Board-Folk/TRS80IJP/Extras/TRSG3Mod/images/g3modboards_large.jpg

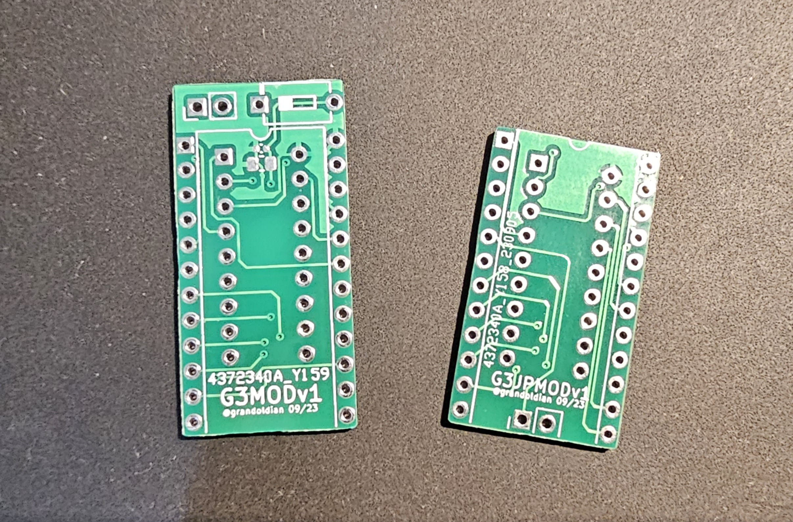
Extras/TRSG3Mod/images/g3modboards_large.jpg
