Board-Folk/TRS80IJP/v1.1/Kicad/TRS80IJP_CPU.kicad_sch

## KiCad design v1.1/Kicad/TRS80IJP_CPU.kicad_sch (2023-09-25)

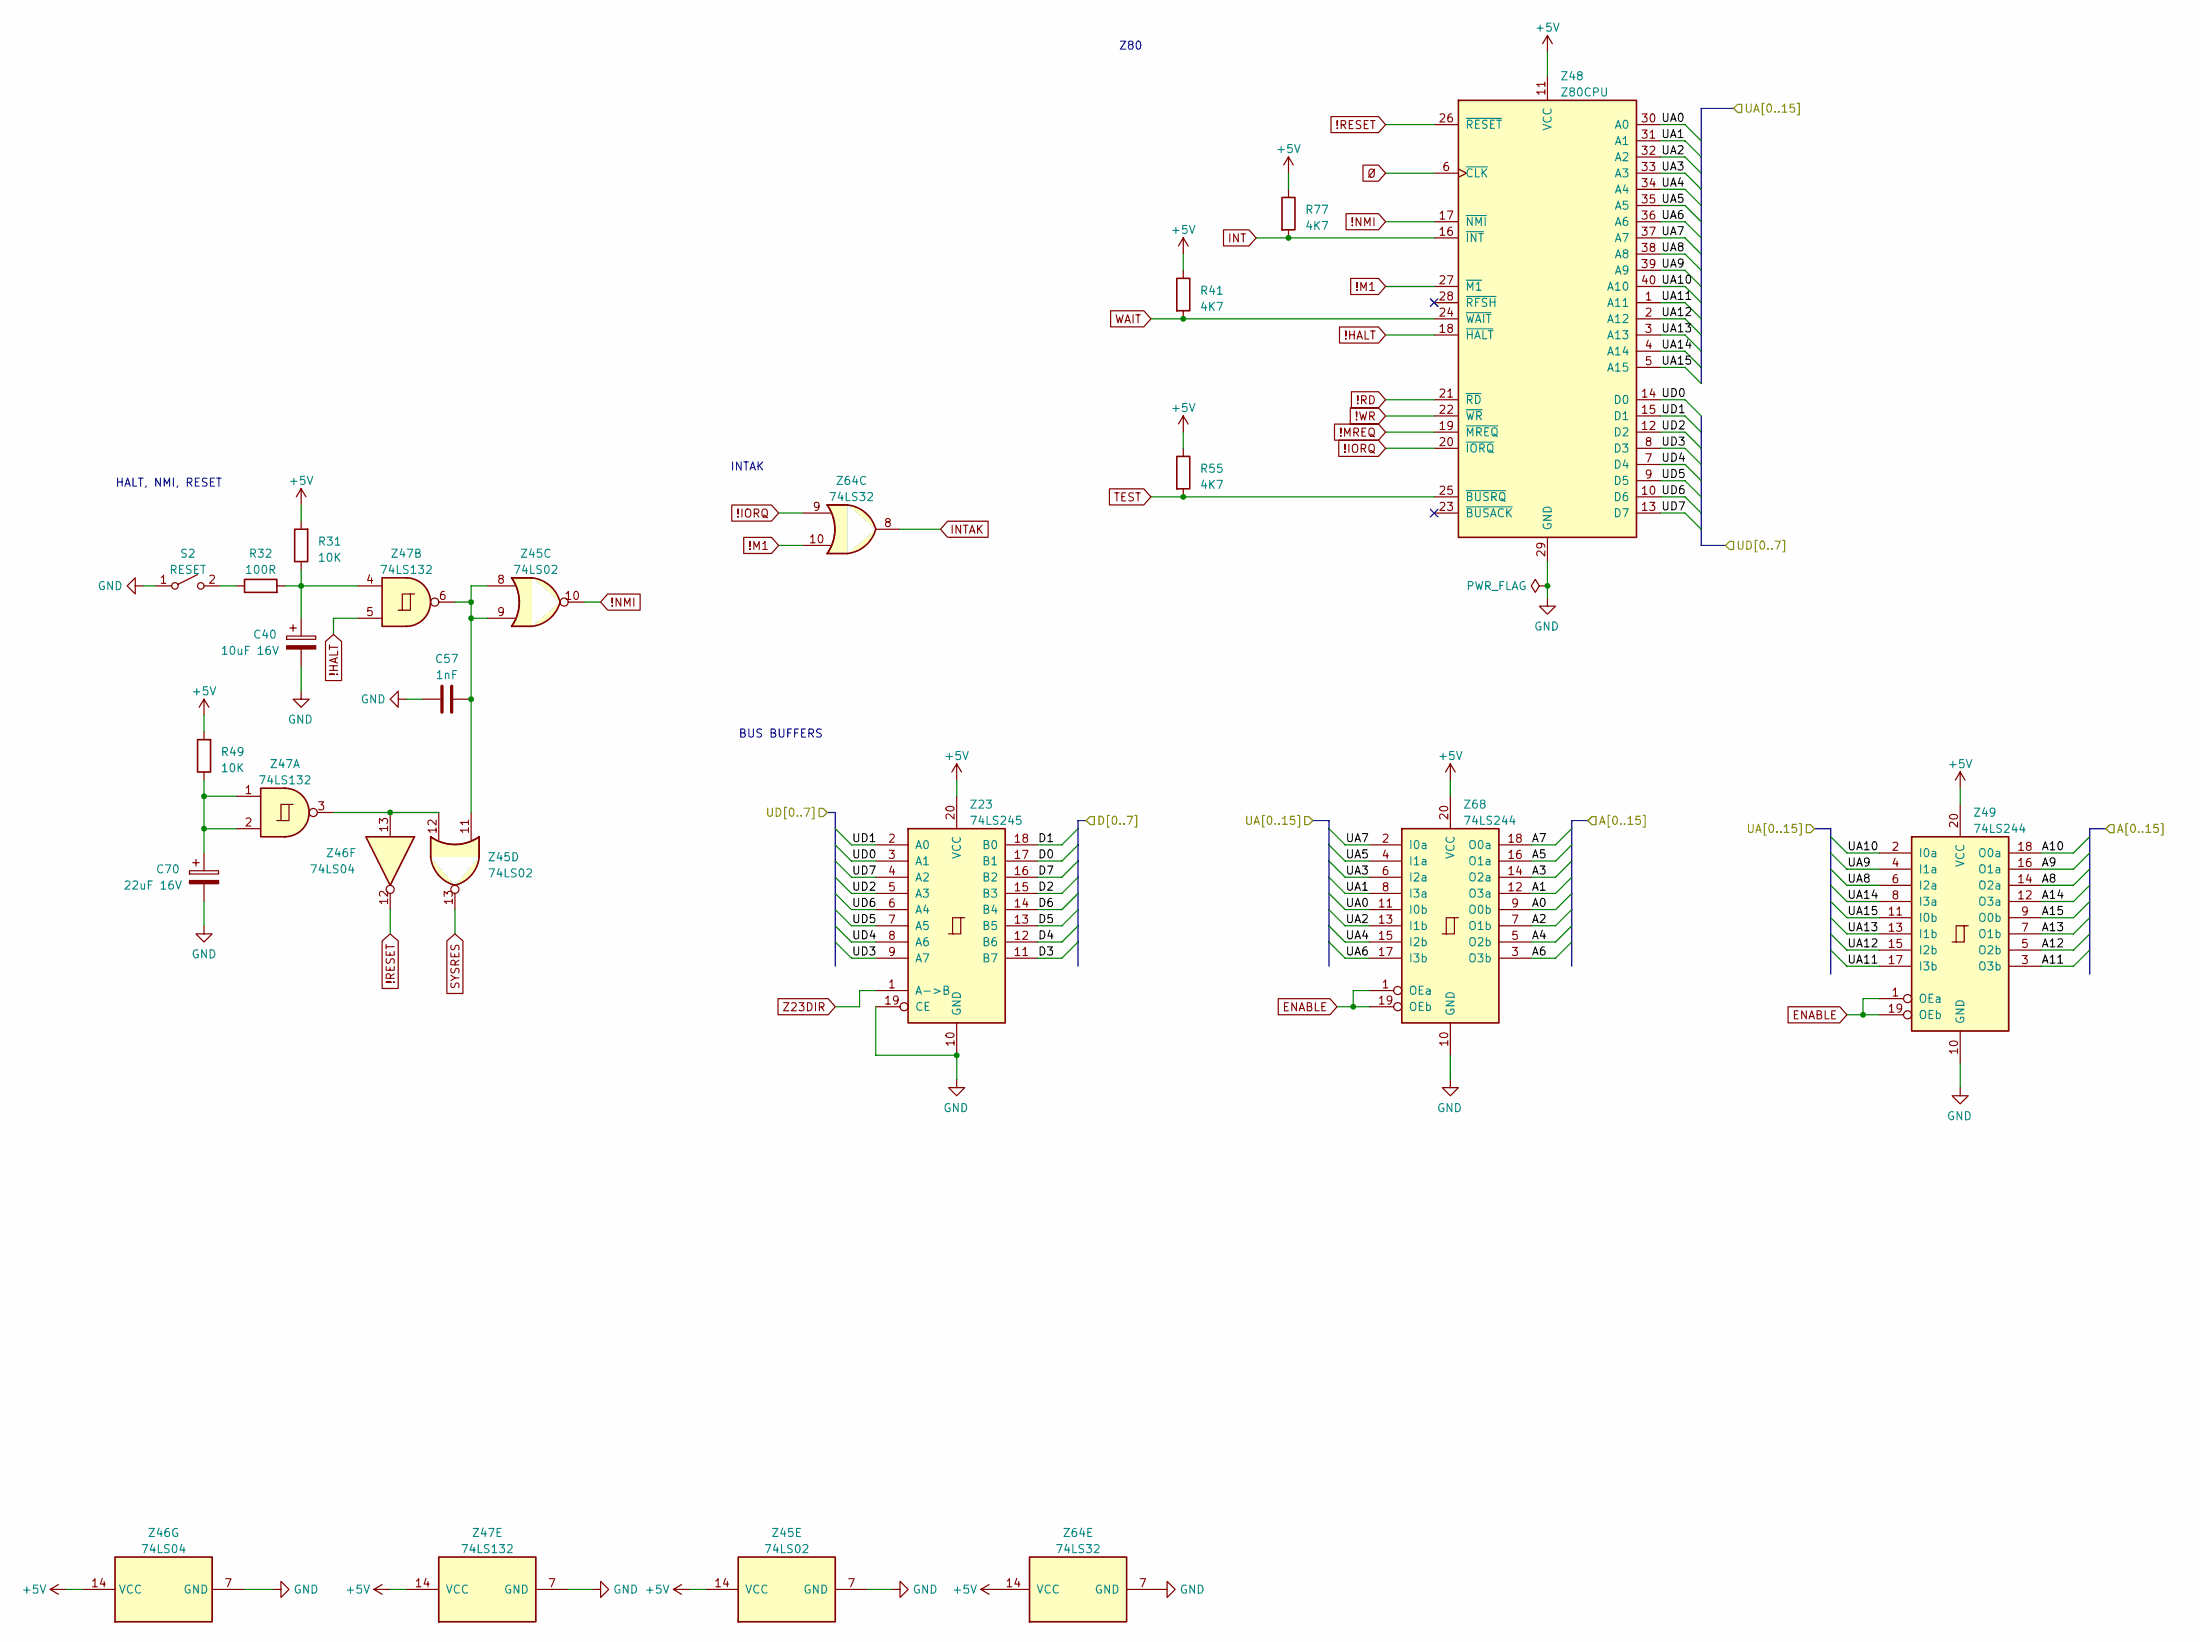
[picture p12: schematic TRS80IJP_CPU.kicad_sch]

Parts:
C40: 10uF 16V; CP_Radial_D5.0mm_P2.50mm
C57: 1nF; Ceramic Disc 2.5mm
C70: 22uF 16V; CP_Radial_D5.0mm_P2.50mm
R31, R49: 10K; Resistor 10.16mm
R32: 100R; Resistor 10.16mm
R41, R55, R77: 4K7; Resistor 10.16mm
S2: RESET; S2
Z23: 74LS245; DIP-20_W7.62mm
Z45: 74LS02; DIP-14_W7.62mm
Z46: 74LS04; DIP-14_W7.62mm
Z47: 74LS132; DIP-14_W7.62mm
Z48: Z80CPU; DIP-40_W15.24mm
Z49, Z68: 74LS244; DIP-20_W7.62mm
Z64: 74LS32; DIP-14_W7.62mm

Connections:
!HALT: Z47.5, Z48.18 (~HALT)
!IORQ: Z48.20 (~IORQ), Z64.9
!M1: Z48.27 (~M1), Z64.10
!MREQ: Z48.19 (~MREQ)
!NMI: Z45.10, Z48.17 (~NMI)
!RD: Z48.21 (~RD)
!RESET: Z46.12, Z48.26 (~RESET)
!WR: Z48.22 (~WR)
+5V: R31.2, R41.1, R49.2, R55.1, R77.1, Z23.20 (VCC), Z45.14 (VCC), Z46.14 (VCC), Z47.14 (VCC), Z48.11 (VCC), Z49.20 (VCC), Z64.14 (VCC), Z68.20 (VCC)
A0: Z68.9 (O0b)
A1: Z68.12 (O3a)
A2: Z68.7 (O1b)
A3: Z68.14 (O2a)
A4: Z68.5 (O2b)
A5: Z68.16 (O1a)
A6: Z68.3 (O3b)
A7: Z68.18 (O0a)
A8: Z49.14 (O2a)
A9: Z49.16 (O1a)
A10: Z49.18 (O0a)
A11: Z49.3 (O3b)
A12: Z49.5 (O2b)
A13: Z49.7 (O1b)
A14: Z49.12 (O3a)
A15: Z49.9 (O0b)
D0: Z23.17 (B1)
D1: Z23.18 (B0)
D2: Z23.15 (B3)
D3: Z23.11 (B7)
D4: Z23.12 (B6)
D5: Z23.13 (B5)
D6: Z23.14 (B4)
D7: Z23.16 (B2)
ENABLE: Z49.1 (OEa), Z49.19 (OEb), Z68.1 (OEa), Z68.19 (OEb)
GND: C40.2, C57.2, C70.2, S2.1 (A), Z23.10 (GND), Z23.19 (CE), Z45.7 (GND), Z46.7 (GND), Z47.7 (GND), Z48.29 (GND), Z49.10 (GND), Z64.7 (GND), Z68.10 (GND)
INT: R77.2, Z48.16 (~INT)
INTAK: Z64.8
unnamed: C40.1, R31.1, R32.2, Z47.4
unnamed: C57.1, Z45.8, Z45.9, Z45.11, Z47.6
unnamed: C70.1, R49.1, Z47.1, Z47.2
unnamed: R32.1, S2.2 (B)
unnamed: Z45.12, Z46.13, Z47.3
SYSRES: Z45.13
TEST: R55.2, Z48.25 (~BUSRQ)
UA0: Z48.30 (A0), Z68.11 (I0b)
UA1: Z48.31 (A1), Z68.8 (I3a)
UA2: Z48.32 (A2), Z68.13 (I1b)
UA3: Z48.33 (A3), Z68.6 (I2a)
UA4: Z48.34 (A4), Z68.15 (I2b)
UA5: Z48.35 (A5), Z68.4 (I1a)
UA6: Z48.36 (A6), Z68.17 (I3b)
UA7: Z48.37 (A7), Z68.2 (I0a)
UA8: Z48.38 (A8), Z49.6 (I2a)
UA9: Z48.39 (A9), Z49.4 (I1a)
UA10: Z48.40 (A10), Z49.2 (I0a)
UA11: Z48.1 (A11), Z49.17 (I3b)
UA12: Z48.2 (A12), Z49.15 (I2b)
UA13: Z48.3 (A13), Z49.13 (I1b)
UA14: Z48.4 (A14), Z49.8 (I3a)
UA15: Z48.5 (A15), Z49.11 (I0b)
UD0: Z23.3 (A1), Z48.14 (D0)
UD1: Z23.2 (A0), Z48.15 (D1)
UD2: Z23.5 (A3), Z48.12 (D2)
UD3: Z23.9 (A7), Z48.8 (D3)
UD4: Z23.8 (A6), Z48.7 (D4)
UD5: Z23.7 (A5), Z48.9 (D5)
UD6: Z23.6 (A4), Z48.10 (D6)
UD7: Z23.4 (A2), Z48.13 (D7)
WAIT: R41.2, Z48.24 (~WAIT)
Z23DIR: Z23.1 (A->B)
Ø: Z48.6 (~CLK)

Notes on the sheet:
INTAK
Z80
HALT, NMI, RESET
BUS BUFFERS
