Board-Folk/TRS80IJP/v1.1/Kicad/TRS80IJP_KEYBOARD.kicad_sch

## KiCad design v1.1/Kicad/TRS80IJP_KEYBOARD.kicad_sch (2023-09-25)

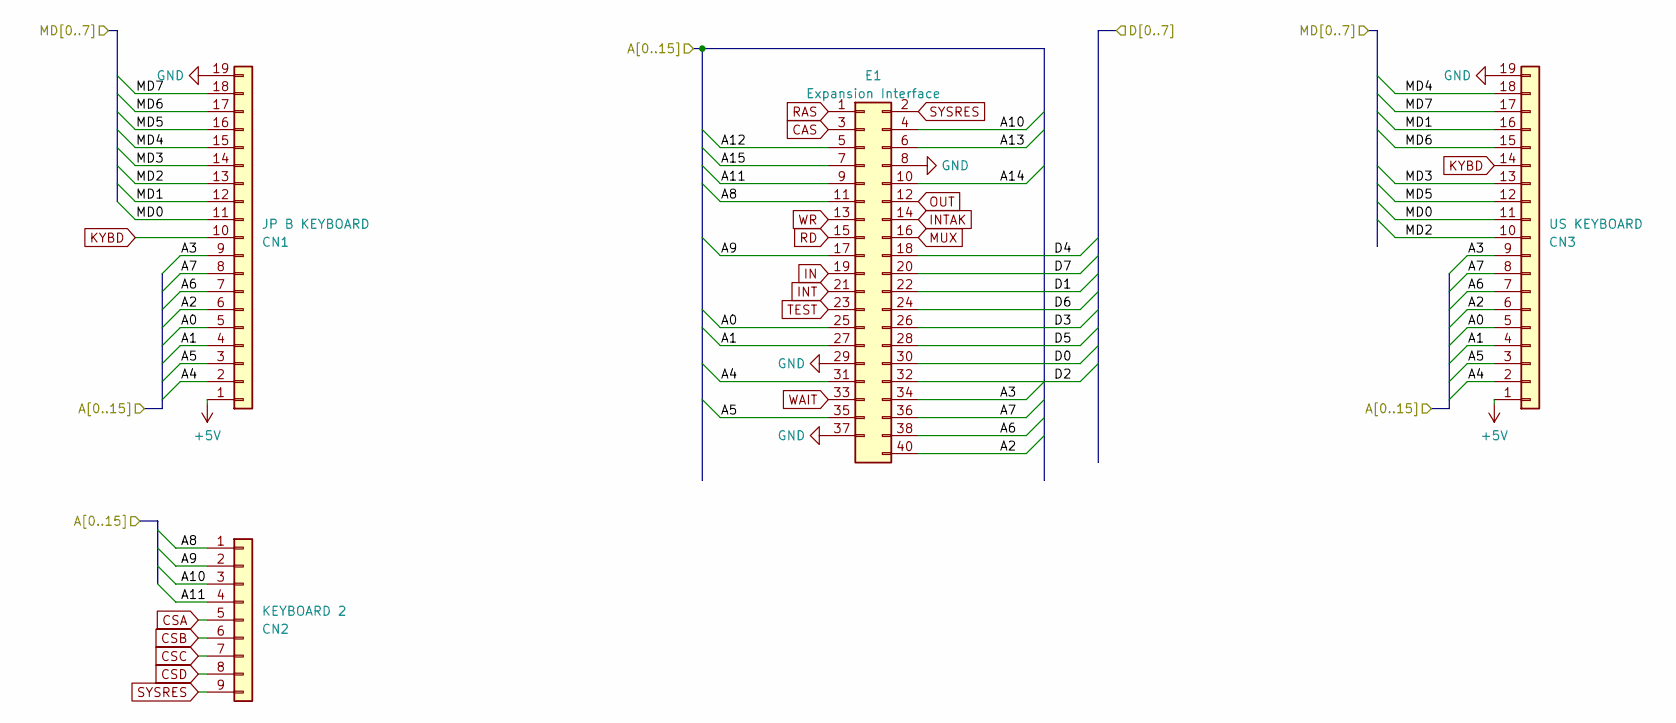
[picture p13: schematic TRS80IJP_KEYBOARD.kicad_sch]

Parts:
CN1: JP B KEYBOARD; Keyboard JP
CN2: KEYBOARD 2; CN2
CN3: US KEYBOARD; Keyboard JP
E1: Expansion Interface; TRS80IEdgeConnector

Connections:
+5V: CN1.1, CN3.1
A0: CN1.5, CN3.5, E1.25
A1: CN1.4, CN3.4, E1.27
A2: CN1.6, CN3.6, E1.40
A3: CN1.9, CN3.9, E1.34
A4: CN1.2, CN3.2, E1.31
A5: CN1.3, CN3.3, E1.35
A6: CN1.7, CN3.7, E1.38
A7: CN1.8, CN3.8, E1.36
A8: CN2.1, E1.11
A9: CN2.2, E1.17
A10: CN2.3, E1.4
A11: CN2.4, E1.9
A12: E1.5
A13: E1.6
A14: E1.10
A15: E1.7
CAS: E1.3
CSA: CN2.5
CSB: CN2.6
CSC: CN2.7
CSD: CN2.8
D0: E1.30
D1: E1.22
D2: E1.32
D3: E1.26
D4: E1.18
D5: E1.28
D6: E1.24
D7: E1.20
GND: CN1.19, CN3.19, E1.8, E1.29, E1.37
IN: E1.19
INT: E1.21
INTAK: E1.14
KYBD: CN1.10, CN3.14
MD0: CN1.11, CN3.11
MD1: CN1.12, CN3.16
MD2: CN1.13, CN3.10
MD3: CN1.14, CN3.13
MD4: CN1.15, CN3.18
MD5: CN1.16, CN3.12
MD6: CN1.17, CN3.15
MD7: CN1.18, CN3.17
MUX: E1.16
OUT: E1.12
RAS: E1.1
RD: E1.15
SYSRES: CN2.9, E1.2
TEST: E1.23
WAIT: E1.33
WR: E1.13
