Board-Folk/TRS80IJP/v1.1/Kicad/TRS80IJP_MEMORY.kicad_sch

## KiCad design v1.1/Kicad/TRS80IJP_MEMORY.kicad_sch (2023-08-20)

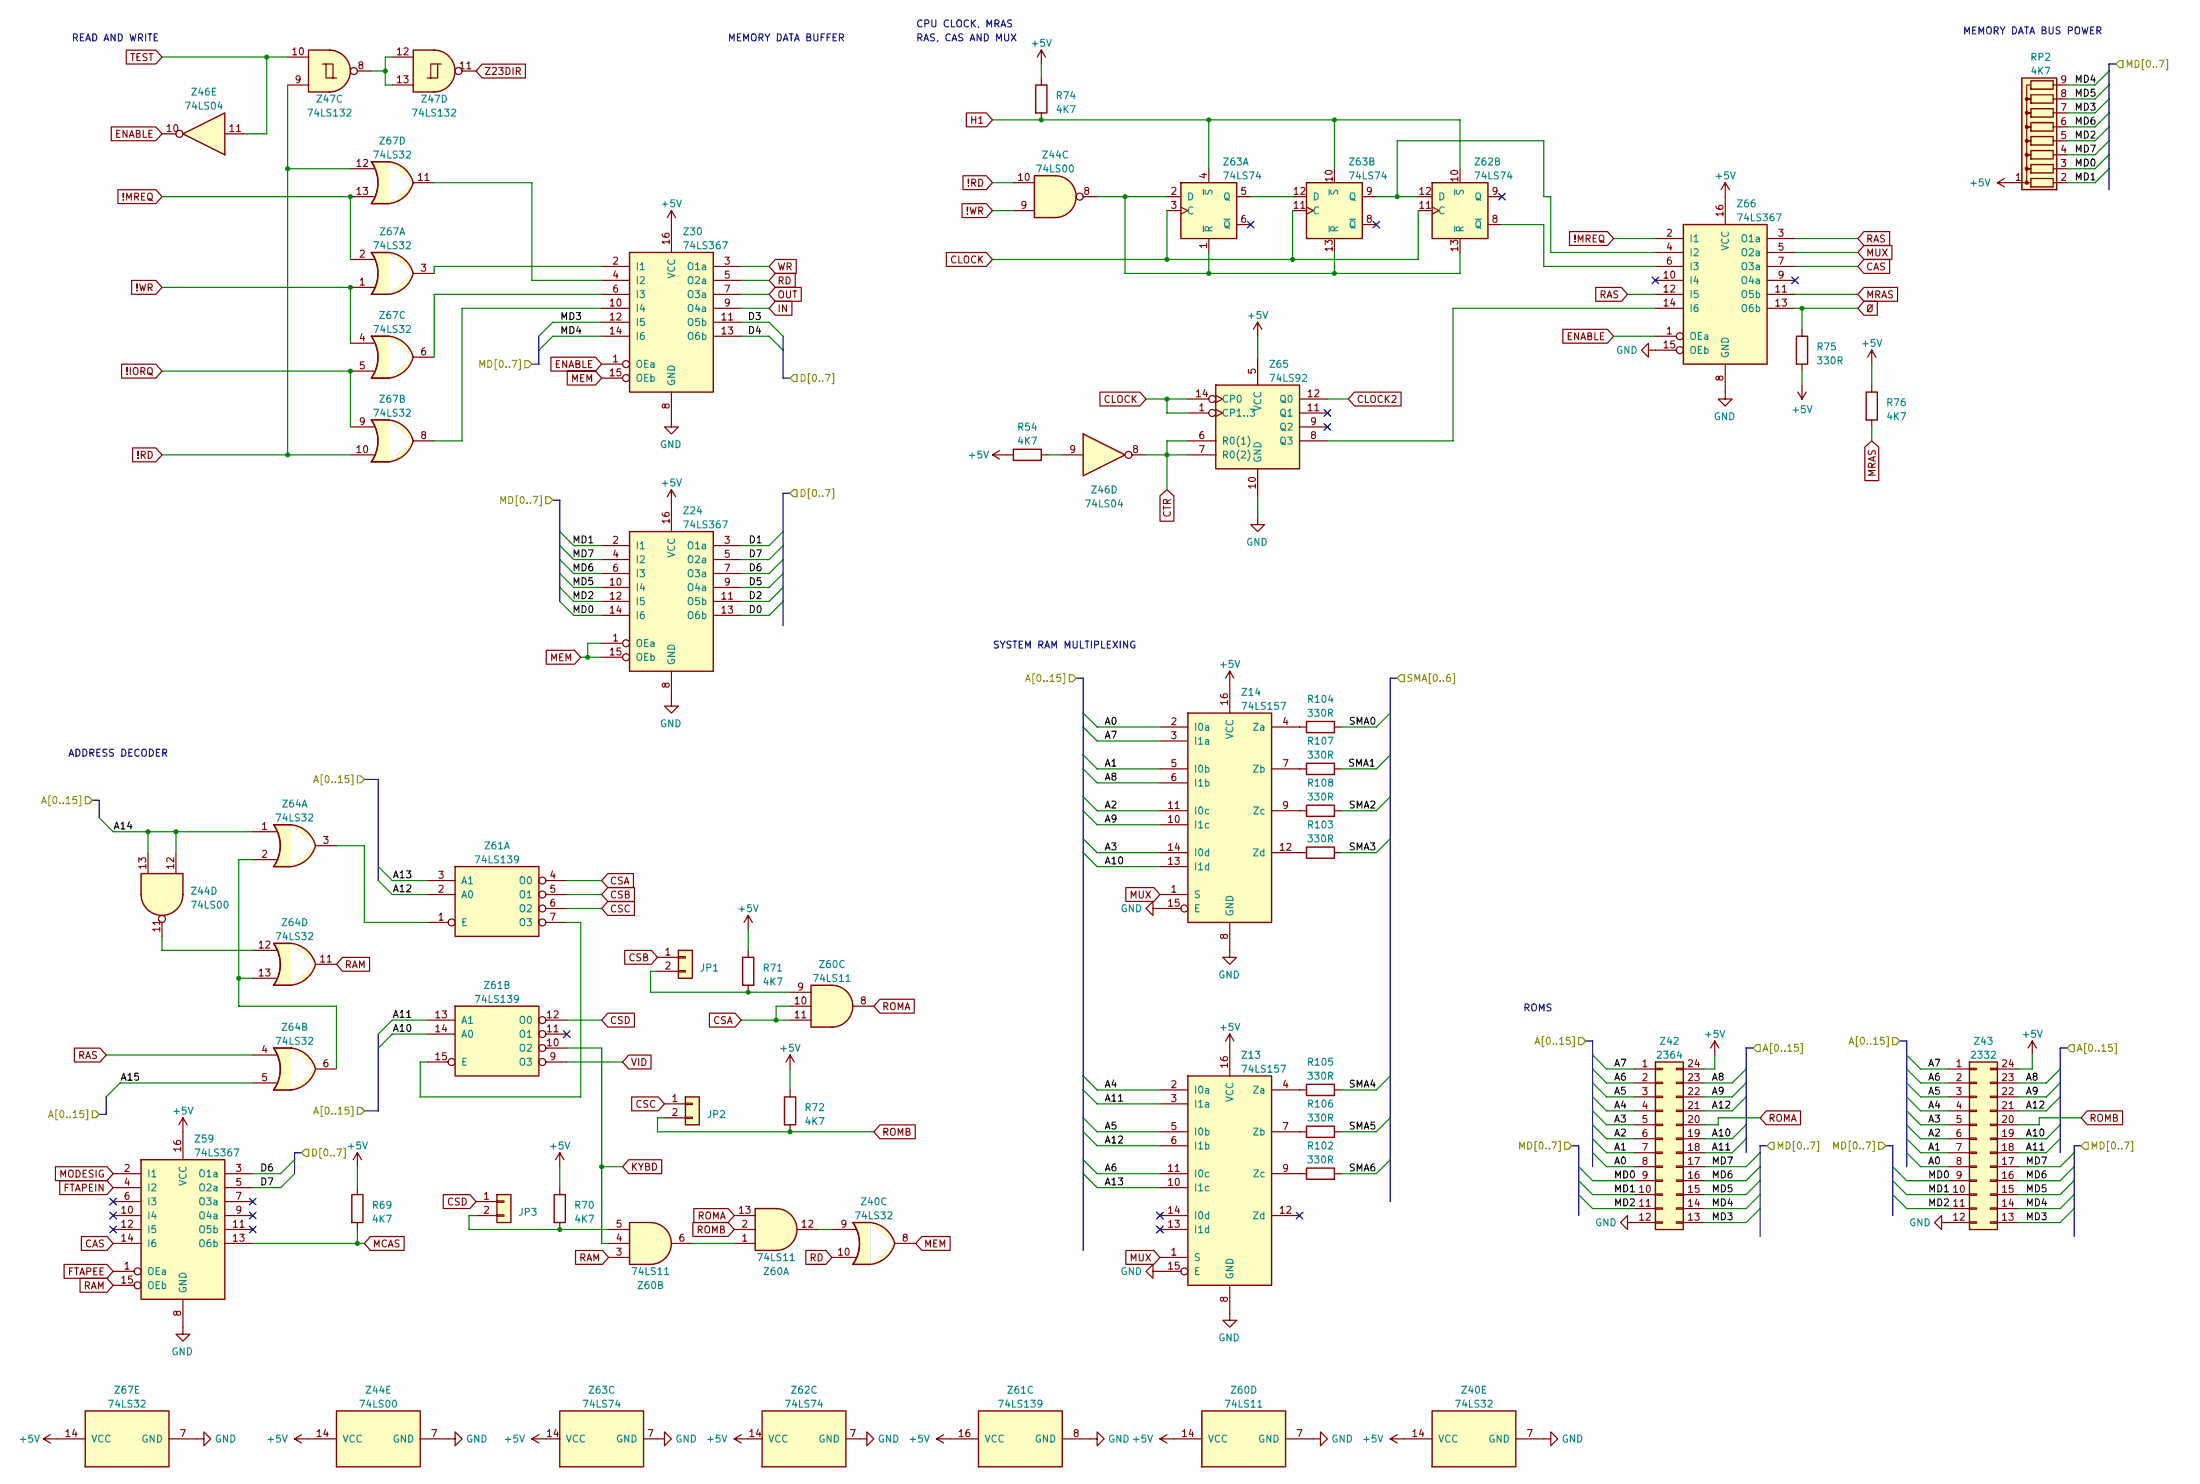
[picture p14: schematic TRS80IJP_MEMORY.kicad_sch]

Parts:
JP1, JP2, JP3: JP1; Wire Jumper
R54, R69, R70, R71, R72, R74, R76: 4K7; Resistor 10.16mm
R75, R102, R103, R104, R105, R106, R107, R108: 330R; Resistor 10.16mm
RP2: 4K7; R_Array_SIP9
Z13, Z14: 74LS157; DIP-16_W7.62mm
Z24, Z30, Z59, Z66: 74LS367; DIP-16_W7.62mm
Z40, Z64, Z67: 74LS32; DIP-14_W7.62mm
Z42: 2364; DIP-24_W15.24mm
Z43: 2332; DIP-24_W15.24mm
Z44: 74LS00; DIP-14_W7.62mm
Z46: 74LS04; DIP-14_W7.62mm
Z47: 74LS132; DIP-14_W7.62mm
Z60: 74LS11; DIP-14_W7.62mm
Z61: 74LS139; DIP-16_W7.62mm
Z62, Z63: 74LS74; DIP-14_W7.62mm
Z65: 74LS92; DIP-14_W7.62mm

Connections:
!IORQ: Z67.5, Z67.9
!MREQ: Z66.2 (I1), Z67.2, Z67.13
!RD: Z44.10, Z47.9, Z67.10, Z67.12
!WR: Z44.9, Z67.1, Z67.4
+5V: R54.1, R69.1, R70.1, R71.1, R72.1, R74.1, R75.2, R76.1, RP2.1 (common), Z13.16 (VCC), Z14.16 (VCC), Z24.16 (VCC), Z30.16 (VCC), Z40.14 (VCC), Z42.24, Z43.24, Z44.14 (VCC), Z59.16 (VCC), Z60.14 (VCC), Z61.16 (VCC), Z62.14 (VCC), Z63.14 (VCC), Z65.5 (VCC), Z66.16 (VCC), Z67.14 (VCC)
A0: Z14.2 (I0a), Z42.8, Z43.8
A1: Z14.5 (I0b), Z42.7, Z43.7
A2: Z14.11 (I0c), Z42.6, Z43.6
A3: Z14.14 (I0d), Z42.5, Z43.5
A4: Z13.2 (I0a), Z42.4, Z43.4
A5: Z13.5 (I0b), Z42.3, Z43.3
A6: Z13.11 (I0c), Z42.2, Z43.2
A7: Z14.3 (I1a), Z42.1, Z43.1
A8: Z14.6 (I1b), Z42.23, Z43.23
A9: Z14.10 (I1c), Z42.22, Z43.22
A10: Z14.13 (I1d), Z42.19, Z43.19, Z61.14 (A0)
A11: Z13.3 (I1a), Z42.18, Z43.18, Z61.13 (A1)
A12: Z13.6 (I1b), Z42.21, Z43.21, Z61.2 (A0)
A13: Z13.10 (I1c), Z61.3 (A1)
A14: Z44.12, Z44.13, Z64.1
A15: Z64.5
CAS: Z59.14 (I6), Z66.7 (O3a)
CLOCK: Z62.11 (C), Z63.3 (C), Z63.11 (C), Z65.1 (CP1..3), Z65.14 (CP0)
CLOCK2: Z65.12 (Q0)
CSA: Z60.10, Z60.11, Z61.4 (O0)
CSB: JP1.1, Z61.5 (O1)
CSC: JP2.1, Z61.6 (O2)
CSD: JP3.1, Z61.12 (O0)
CTR: Z46.8, Z65.6 (R0(1)), Z65.7 (R0(2))
D0: Z24.13 (O6b)
D1: Z24.3 (O1a)
D2: Z24.11 (O5b)
D3: Z30.11 (O5b)
D4: Z30.13 (O6b)
D5: Z24.9 (O4a)
D6: Z24.7 (O3a), Z59.3 (O1a)
D7: Z24.5 (O2a), Z59.5 (O2a)
ENABLE: Z30.1 (OEa), Z46.10, Z66.1 (OEa)
FTAPEE: Z59.1 (OEa)
FTAPEIN: Z59.4 (I2)
GND: Z13.8 (GND), Z13.15 (E), Z14.8 (GND), Z14.15 (E), Z24.8 (GND), Z30.8 (GND), Z40.7 (GND), Z42.12, Z43.12, Z44.7 (GND), Z59.8 (GND), Z60.7 (GND), Z61.8 (GND), Z62.7 (GND), Z63.7 (GND), Z65.10 (GND), Z66.8 (GND), Z66.15 (OEb), Z67.7 (GND)
H1: R74.2, Z62.10 (~S), Z63.4 (~S), Z63.10 (~S)
IN: Z30.9 (O4a)
KYBD: Z60.4, Z61.10 (O2)
MCAS: R69.2, Z59.13 (O6b)
MD0: RP2.3 (R2), Z24.14 (I6), Z42.9, Z43.9
MD1: RP2.2 (R1), Z24.2 (I1), Z42.10, Z43.10
MD2: RP2.5 (R4), Z24.12 (I5), Z42.11, Z43.11
MD3: RP2.7 (R6), Z30.12 (I5), Z42.13, Z43.13
MD4: RP2.9 (R8), Z30.14 (I6), Z42.14, Z43.14
MD5: RP2.8 (R7), Z24.10 (I4), Z42.15, Z43.15
MD6: RP2.6 (R5), Z24.6 (I3), Z42.16, Z43.16
MD7: RP2.4 (R3), Z24.4 (I2), Z42.17, Z43.17
MEM: Z24.1 (OEa), Z24.15 (OEb), Z30.15 (OEb), Z40.8
MODESIG: Z59.2 (I1)
MRAS: R76.2, Z66.11 (O5b)
MUX: Z13.1 (S), Z14.1 (S), Z66.5 (O2a)
unnamed: JP1.2, R71.2, Z60.9
unnamed: JP3.2, R70.2, Z60.5
unnamed: R54.2, Z46.9
unnamed: R102.1, Z13.9 (Zc)
unnamed: R103.1, Z14.12 (Zd)
unnamed: R104.1, Z14.4 (Za)
unnamed: R105.1, Z13.4 (Za)
unnamed: R106.1, Z13.7 (Zb)
unnamed: R107.1, Z14.7 (Zb)
unnamed: R108.1, Z14.9 (Zc)
unnamed: Z30.2 (I1), Z67.3
unnamed: Z30.4 (I2), Z67.11
unnamed: Z30.6 (I3), Z67.6
unnamed: Z30.10 (I4), Z67.8
unnamed: Z40.9, Z60.12
unnamed: Z44.8, Z62.13 (~R), Z63.1 (~R), Z63.2 (D), Z63.13 (~R)
unnamed: Z44.11, Z64.12
unnamed: Z47.8, Z47.12, Z47.13
unnamed: Z60.1, Z60.6
unnamed: Z61.1 (E), Z64.3
unnamed: Z61.7 (O3), Z61.15 (E)
unnamed: Z62.8 (~Q), Z66.6 (I3)
unnamed: Z62.12 (D), Z63.9 (Q), Z66.4 (I2)
unnamed: Z63.5 (Q), Z63.12 (D)
unnamed: Z64.2, Z64.6, Z64.13
unnamed: Z65.8 (Q3), Z66.14 (I6)
OUT: Z30.7 (O3a)
RAM: Z59.15 (OEb), Z60.3, Z64.11
RAS: Z64.4, Z66.3 (O1a), Z66.12 (I5)
RD: Z30.5 (O2a), Z40.10
ROMA: Z42.20, Z60.8, Z60.13
ROMB: JP2.2, R72.2, Z43.20, Z60.2
SMA0: R104.2
SMA1: R107.2
SMA2: R108.2
SMA3: R103.2
SMA4: R105.2
SMA5: R106.2
SMA6: R102.2
TEST: Z46.11, Z47.10
VID: Z61.9 (O3)
WR: Z30.3 (O1a)
Z23DIR: Z47.11
Ø: R75.1, Z66.13 (O6b)

Notes on the sheet:
ADDRESS DECODER
READ AND WRITE
ROMS
MEMORY DATA BUS POWER
CPU CLOCK, MRAS
MEMORY DATA BUFFER
RAS, CAS AND MUX
SYSTEM RAM MULTIPLEXING
