Board-Folk/TRS80IJP/v1.1/Kicad/TRS80IJP_POWER.kicad_sch

## KiCad design v1.1/Kicad/TRS80IJP_POWER.kicad_sch (2023-09-25)

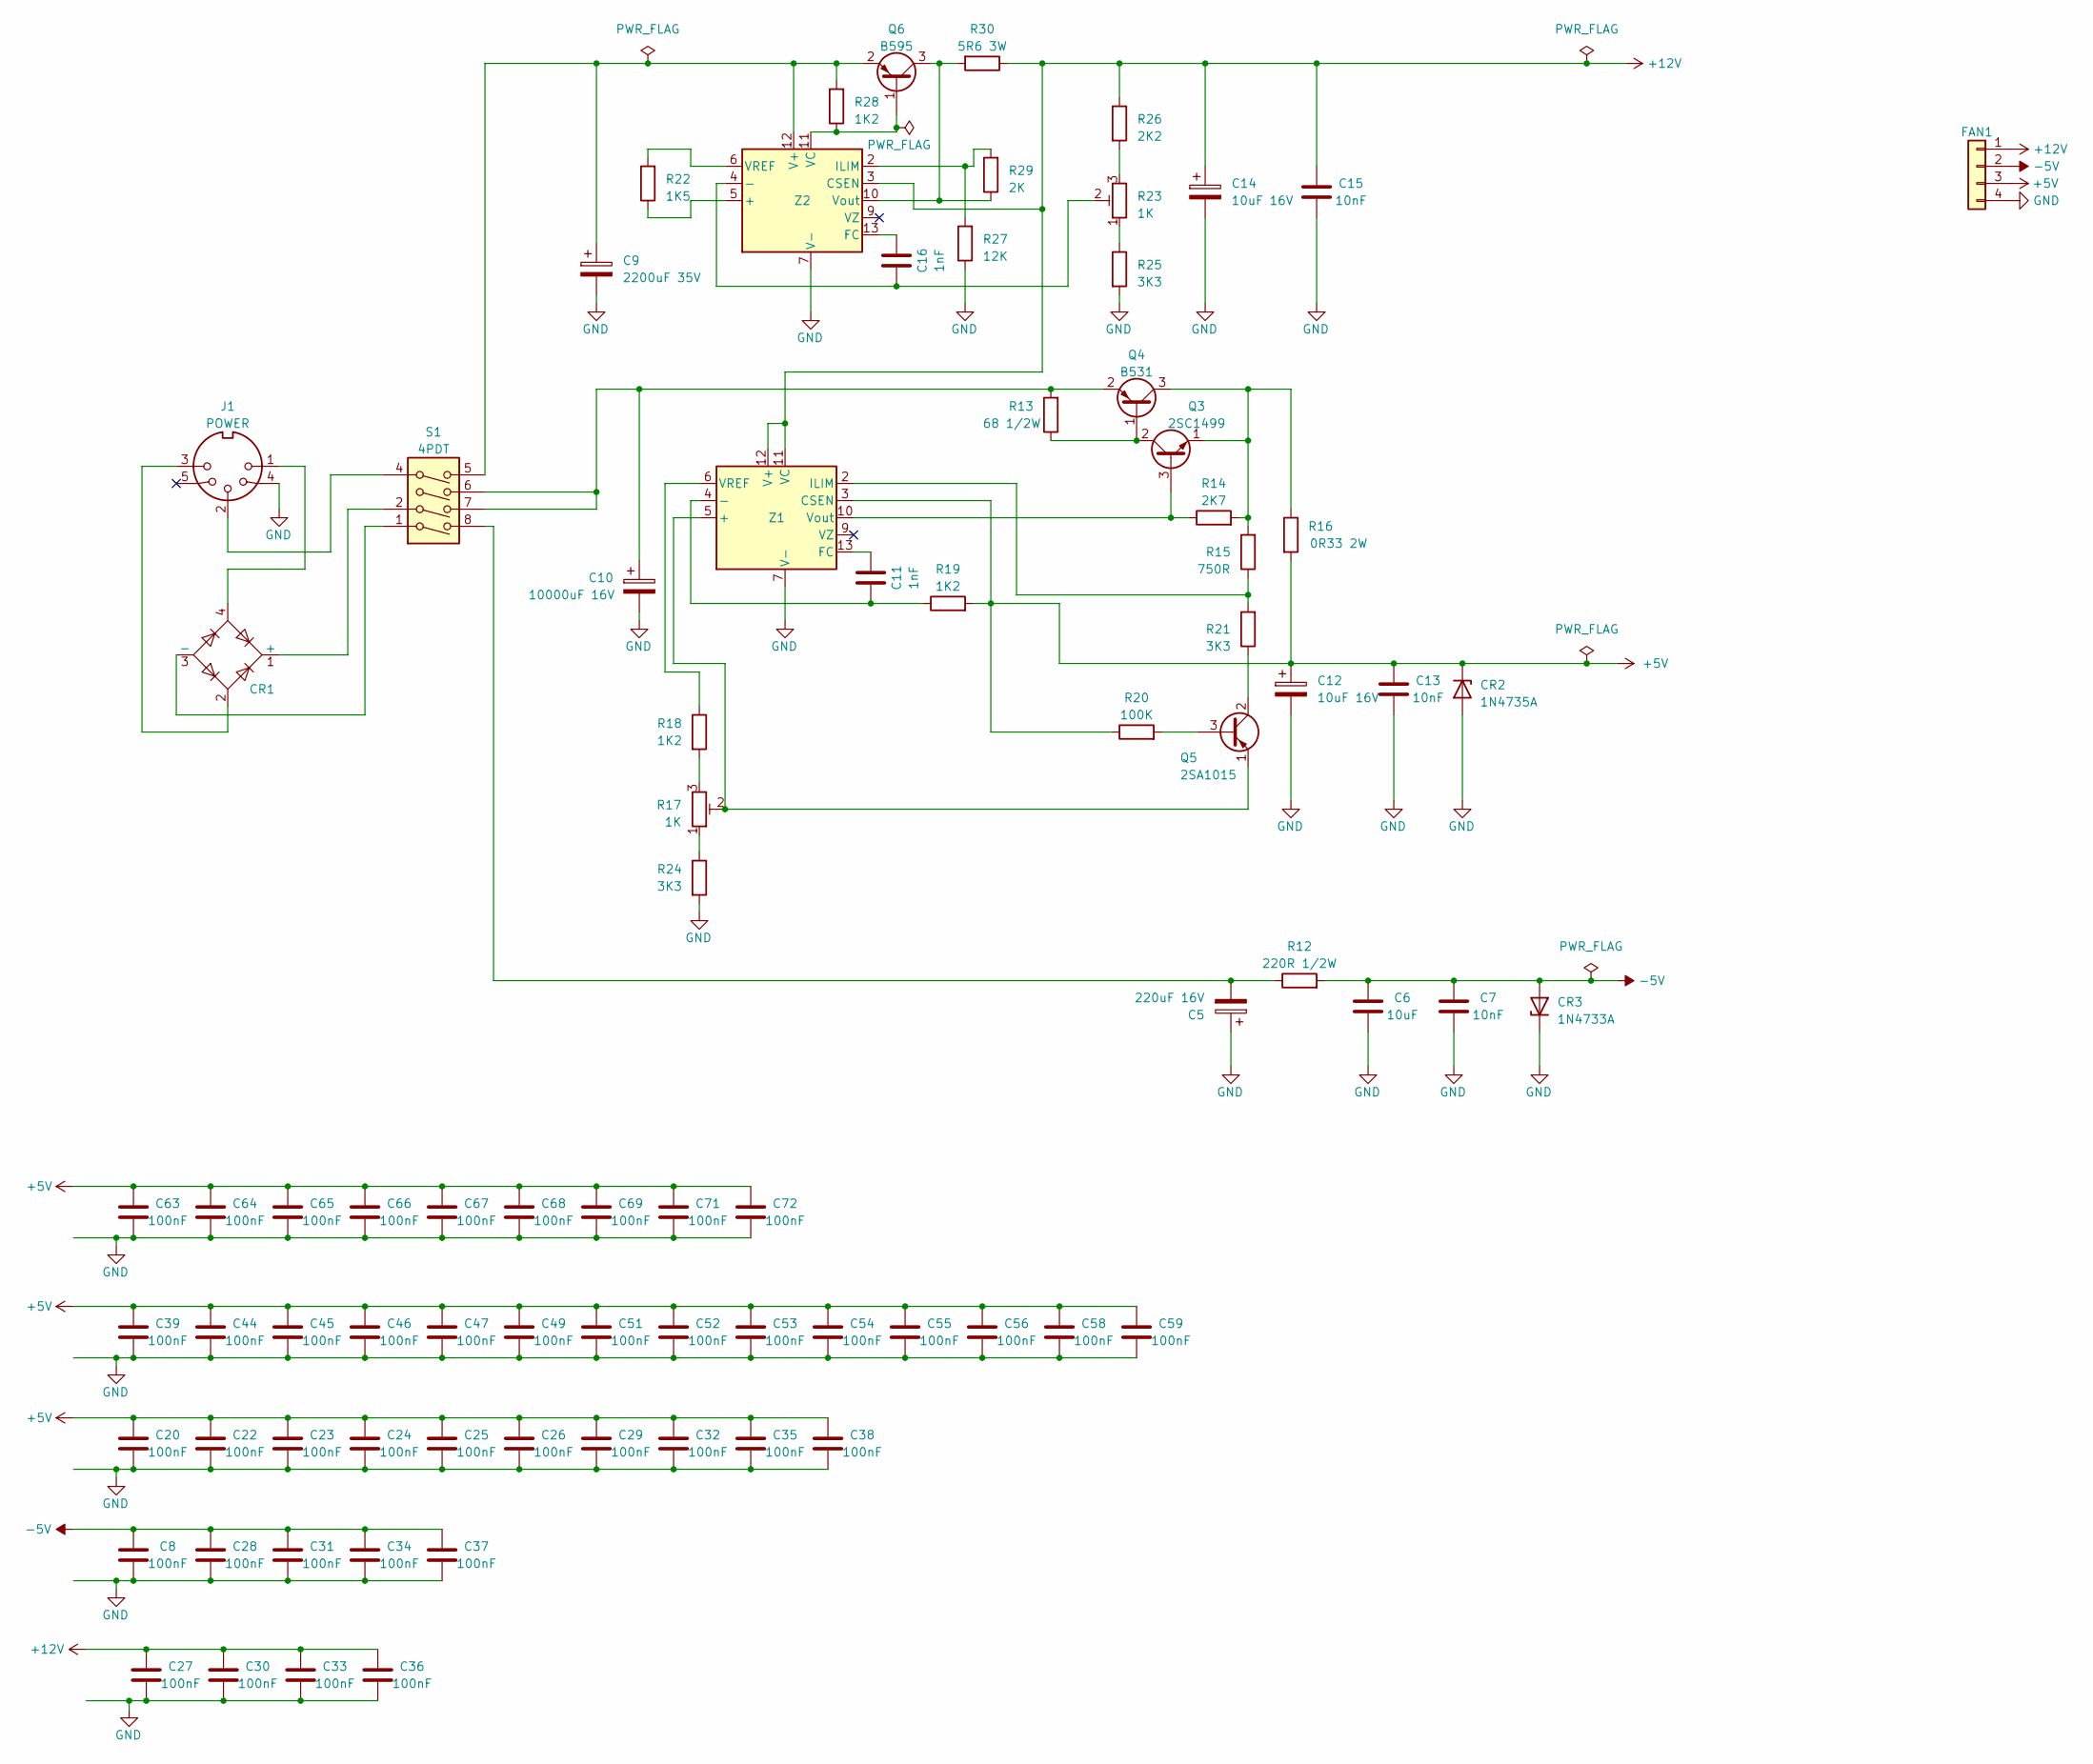
[picture p15: schematic TRS80IJP_POWER.kicad_sch]

Parts:
C5: 220uF 16V; CP_Radial_P5.00mm
C6: 10uF; CP_Radial_D5.0mm_P2.50mm
C7, C13, C15: 10nF; Ceramic Disc 5mm
C8, C20, C22, C23, C24, C25, C26, C27, C28, C29, C30, C31, C32, C33, C34, C35, C36, C37, C38, C39, C44, C45, C46, C47, C49, C51, C52, C53, C54, C55, C56, C58, C59, C63, C64, C65, C66, C67, C68, C69, C71, C72: 100nF; Ceramic Disc 5mm
C9: 2200uF 35V; CP_Axial_L42.5mm_D20.0mm_P49.00mm
C10: 10000uF 16V; Electroytic Axial 69mm
C11, C16: 1nF; Ceramic Disc 2.5mm
C12, C14: 10uF 16V; CP_Radial_D5.0mm_P2.50mm
CR1: S2V B20; Rectifier
CR2: 1N4735A; Diode 2 15mm
CR3: 1N4733A; Diode CR3
FAN1: FAN; Fan
J1: POWER; J1 - POWER
Q3: 2SC1499; Q3
Q4: B531; Q4 TO-3
Q5: 2SA1015; TO-92_Transistor
Q6: B595; Q6
R12: 220R 1/2W; Resistor 15mm
R13: 68 1/2W; Resistor 15mm
R14: 2K7; Resistor 10.16mm
R15: 750R; Resistor 10.16mm
R16: 0R33 2W; Resistor 23mm
R17: 1K; Pot-R17
R18, R19, R28: 1K2; Resistor 10.16mm
R20: 100K; Resistor 10.16mm
R21, R24, R25: 3K3; Resistor 10.16mm
R22: 1K5; Resistor 10.16mm
R23: 1K; Pot
R26: 2K2; Resistor 10.16mm
R27: 12K; Resistor 10.16mm
R29: 2K; Resistor 10.16mm
R30: 5R6 3W; Resistor 30mm
S1: 4PDT; Switch
Z1, Z2: LM723_DIP14; DIP-14_W7.62mm

Connections:
+5V: C12.1, C13.2, C20.2, C22.2, C23.2, C24.2, C25.2, C26.2, C29.2, C32.2, C35.2, C38.2, C39.2, C44.2, C45.2, C46.2, C47.2, C49.2, C51.2, C52.2, C53.2, C54.2, C55.2, C56.2, C58.2, C59.2, C63.2, C64.2, C65.2, C66.2, C67.2, C68.2, C69.2, C71.2, C72.2, CR2.1 (K), FAN1.3, R16.2, R19.2, R20.1, Z1.3 (CSEN)
+12V: C14.1, C15.2, C27.2, C30.2, C33.2, C36.2, FAN1.1, R26.1, R30.1, Z1.11 (VC), Z1.12 (V+), Z2.3 (CSEN)
-5V: C6.2, C7.2, C8.2, C28.2, C31.2, C34.2, C37.2, CR3.2 (A), FAN1.2, R12.2
GND: C5.1, C6.1, C7.1, C8.1, C9.2, C10.2, C12.2, C13.1, C14.2, C15.1, C20.1, C22.1, C23.1, C24.1, C25.1, C26.1, C27.1, C28.1, C29.1, C30.1, C31.1, C32.1, C33.1, C34.1, C35.1, C36.1, C37.1, C38.1, C39.1, C44.1, C45.1, C46.1, C47.1, C49.1, C51.1, C52.1, C53.1, C54.1, C55.1, C56.1, C58.1, C59.1, C63.1, C64.1, C65.1, C66.1, C67.1, C68.1, C69.1, C71.1, C72.1, CR2.2 (A), CR3.1 (K), FAN1.4, J1.4, R24.2, R25.2, R27.1, Z1.7 (V-), Z2.7 (V-)
unnamed: C5.2, R12.1, S1.8
unnamed: C9.1, Q6.2 (E), R28.2, S1.5, Z2.12 (V+)
unnamed: C10.1, Q4.2 (E), R13.2, S1.6, S1.7
unnamed: C11.1, R19.1, Z1.4 (-)
unnamed: C11.2, Z1.13 (FC)
unnamed: C16.1, R23.2, Z2.4 (-)
unnamed: C16.2, Z2.13 (FC)
unnamed: CR1.1 (+), S1.2
unnamed: CR1.2, J1.3
unnamed: CR1.3 (-), S1.1
unnamed: CR1.4, J1.1
unnamed: J1.2, S1.4
unnamed: Q3.1 (E), Q4.3 (C), R14.2, R15.2, R16.1
unnamed: Q3.2 (C), Q4.1 (B), R13.1
unnamed: Q3.3 (B), R14.1, Z1.10 (Vout)
unnamed: Q5.1 (E), R17.2, Z1.5 (+)
unnamed: Q5.2 (C), R21.1
unnamed: Q5.3 (B), R20.2
unnamed: Q6.1 (B), R28.1, Z2.11 (VC)
unnamed: Q6.3 (C), R29.1, R30.2, Z2.10 (Vout)
unnamed: R15.1, R21.2, Z1.2 (ILIM)
unnamed: R17.1, R24.1
unnamed: R17.3, R18.2
unnamed: R18.1, Z1.6 (VREF)
unnamed: R22.1, Z2.5 (+)
unnamed: R22.2, Z2.6 (VREF)
unnamed: R23.1, R25.1
unnamed: R23.3, R26.2
unnamed: R27.2, R29.2, Z2.2 (ILIM)
