Board-Folk/TRS80IJP/v1.1/Kicad/TRS80IJP_RAM.kicad_sch

## KiCad design v1.1/Kicad/TRS80IJP_RAM.kicad_sch (2023-08-20)

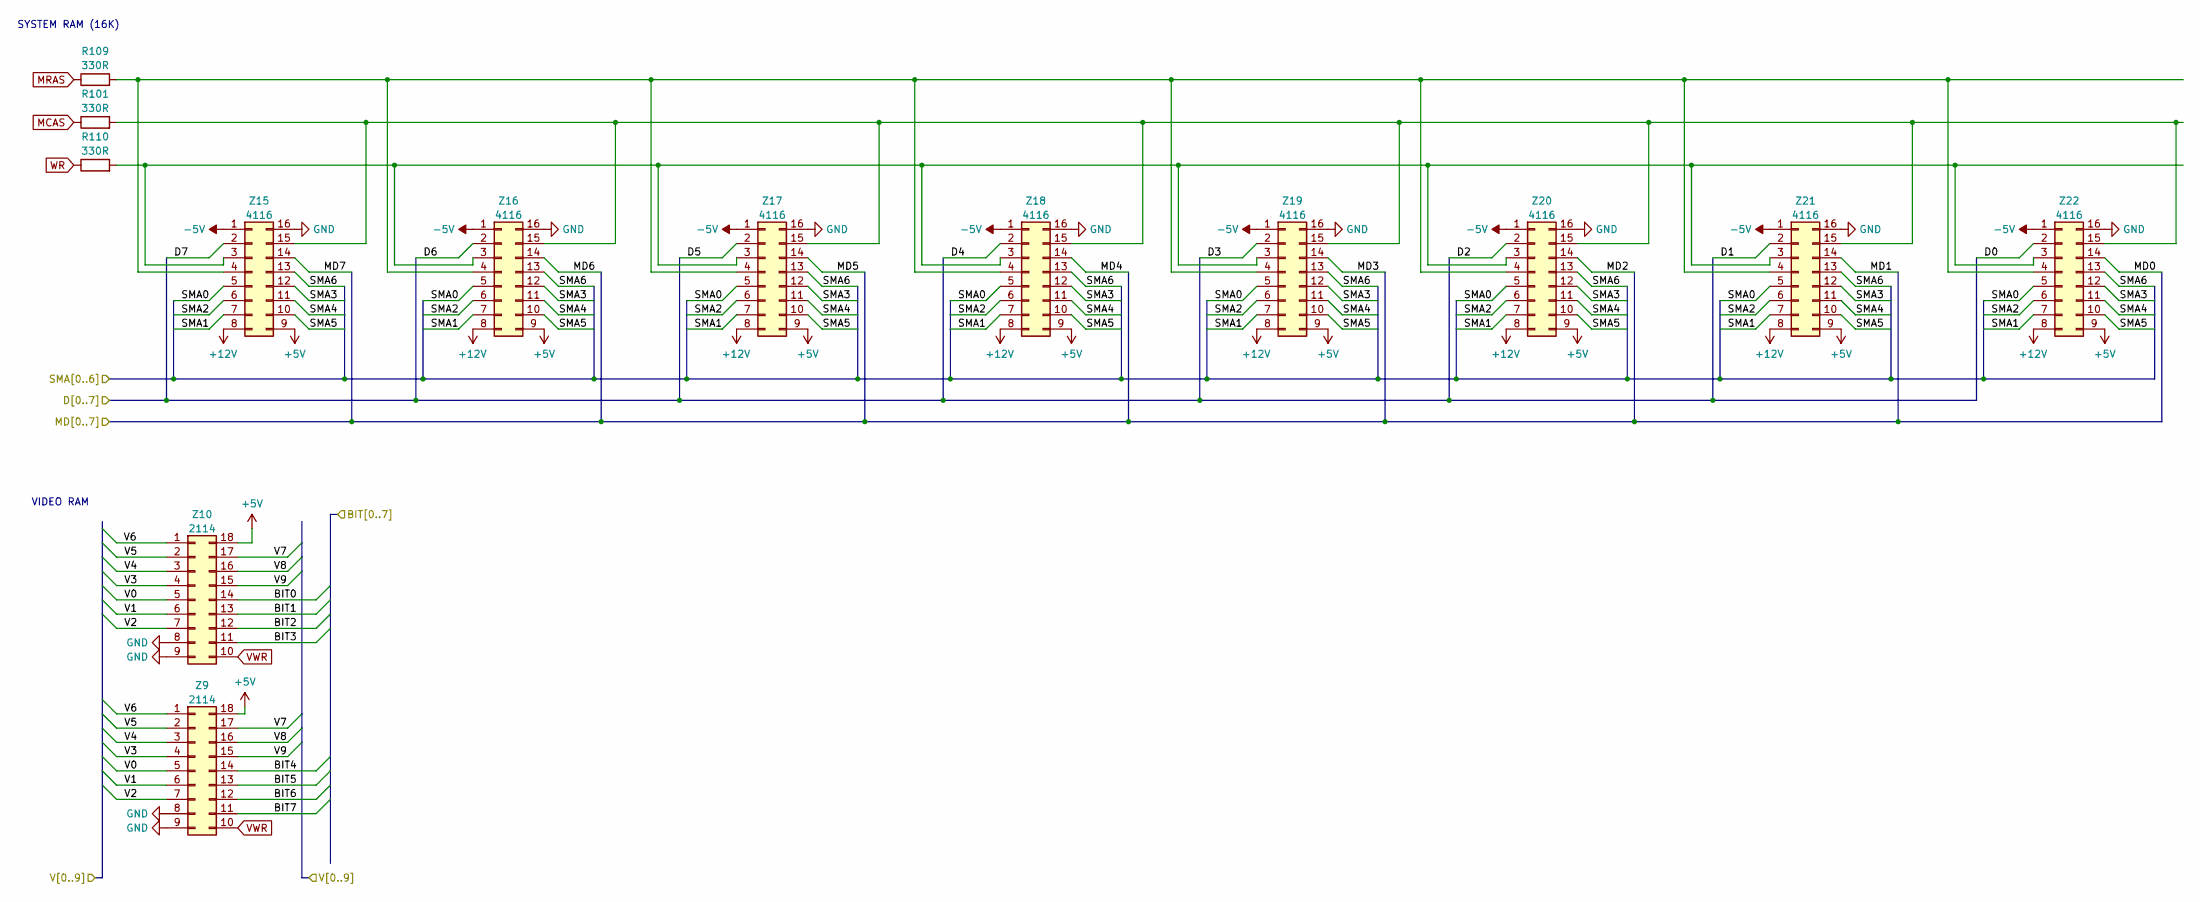
[picture p16: schematic TRS80IJP_RAM.kicad_sch]

Parts:
R101, R109, R110: 330R; Resistor 10.16mm
Z9, Z10: 2114; DIP-18_W7.62mm
Z15, Z16, Z17, Z18, Z19, Z20, Z21, Z22: 4116; DIP-16_W7.62mm

Connections:
+5V: Z9.18, Z10.18, Z15.9, Z16.9, Z17.9, Z18.9, Z19.9, Z20.9, Z21.9, Z22.9
+12V: Z15.8, Z16.8, Z17.8, Z18.8, Z19.8, Z20.8, Z21.8, Z22.8
-5V: Z15.1, Z16.1, Z17.1, Z18.1, Z19.1, Z20.1, Z21.1, Z22.1
BIT0: Z10.14
BIT1: Z10.13
BIT2: Z10.12
BIT3: Z10.11
BIT4: Z9.14
BIT5: Z9.13
BIT6: Z9.12
BIT7: Z9.11
GND: Z9.8, Z9.9, Z10.8, Z10.9, Z15.16, Z16.16, Z17.16, Z18.16, Z19.16, Z20.16, Z21.16, Z22.16
MCAS: R101.1
MRAS: R109.1
unnamed: R101.2, Z15.15, Z16.15, Z17.15, Z18.15, Z19.15, Z20.15, Z21.15, Z22.15
unnamed: R109.2, Z15.4, Z16.4, Z17.4, Z18.4, Z19.4, Z20.4, Z21.4, Z22.4
unnamed: R110.2, Z15.3, Z16.3, Z17.3, Z18.3, Z19.3, Z20.3, Z21.3, Z22.3
V0: Z9.5, Z10.5
V1: Z9.6, Z10.6
V2: Z9.7, Z10.7
V3: Z9.4, Z10.4
V4: Z9.3, Z10.3
V5: Z9.2, Z10.2
V6: Z9.1, Z10.1
V7: Z9.17, Z10.17
V8: Z9.16, Z10.16
V9: Z9.15, Z10.15
VWR: Z9.10, Z10.10
WR: R110.1

Notes on the sheet:
SYSTEM RAM (16K)
VIDEO RAM
