Board-Folk/TRS80IJP/v1.1/Kicad/TRS80IJP_SPARE.kicad_sch

## KiCad design v1.1/Kicad/TRS80IJP_SPARE.kicad_sch (2023-08-20)

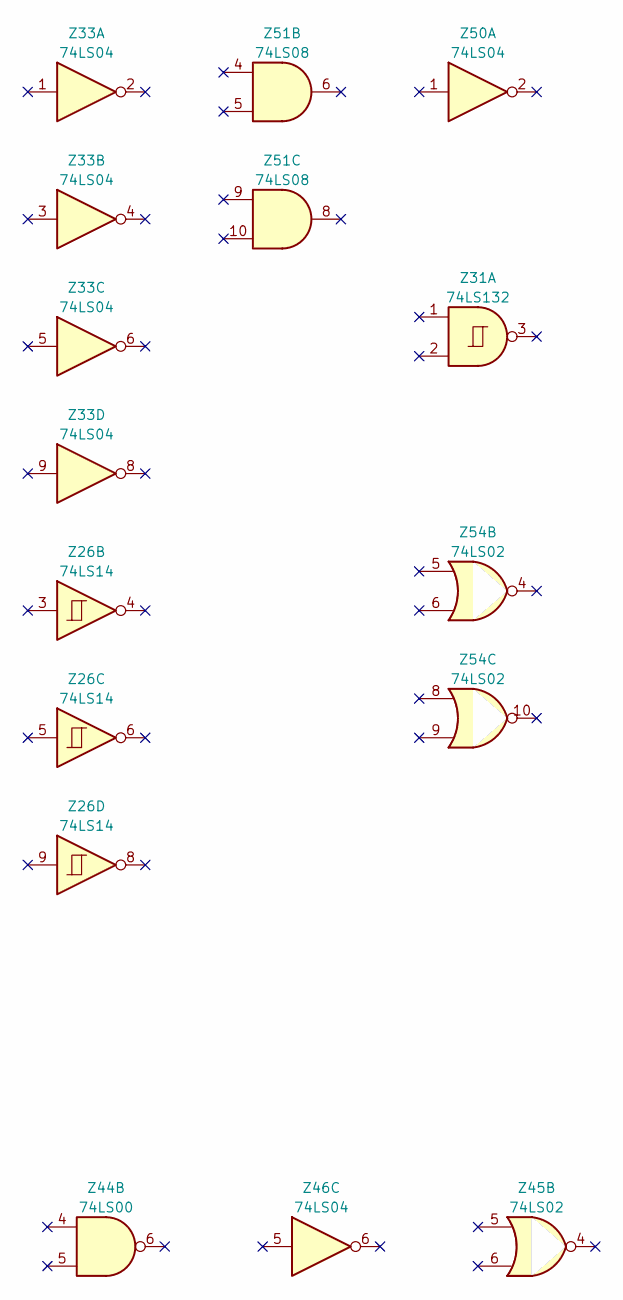
[picture p17: schematic TRS80IJP_SPARE.kicad_sch]

Parts:
Z26: 74LS14; DIP-14_W7.62mm
Z31: 74LS132; DIP-14_W7.62mm
Z33, Z46, Z50: 74LS04; DIP-14_W7.62mm
Z44: 74LS00; DIP-14_W7.62mm
Z45, Z54: 74LS02; DIP-14_W7.62mm
Z51: 74LS08; DIP-14_W7.62mm
