Board-Folk/TRS80IJP/v1.1/Kicad/TRS80IJP_TAPE.kicad_sch

## KiCad design v1.1/Kicad/TRS80IJP_TAPE.kicad_sch (2023-09-25)

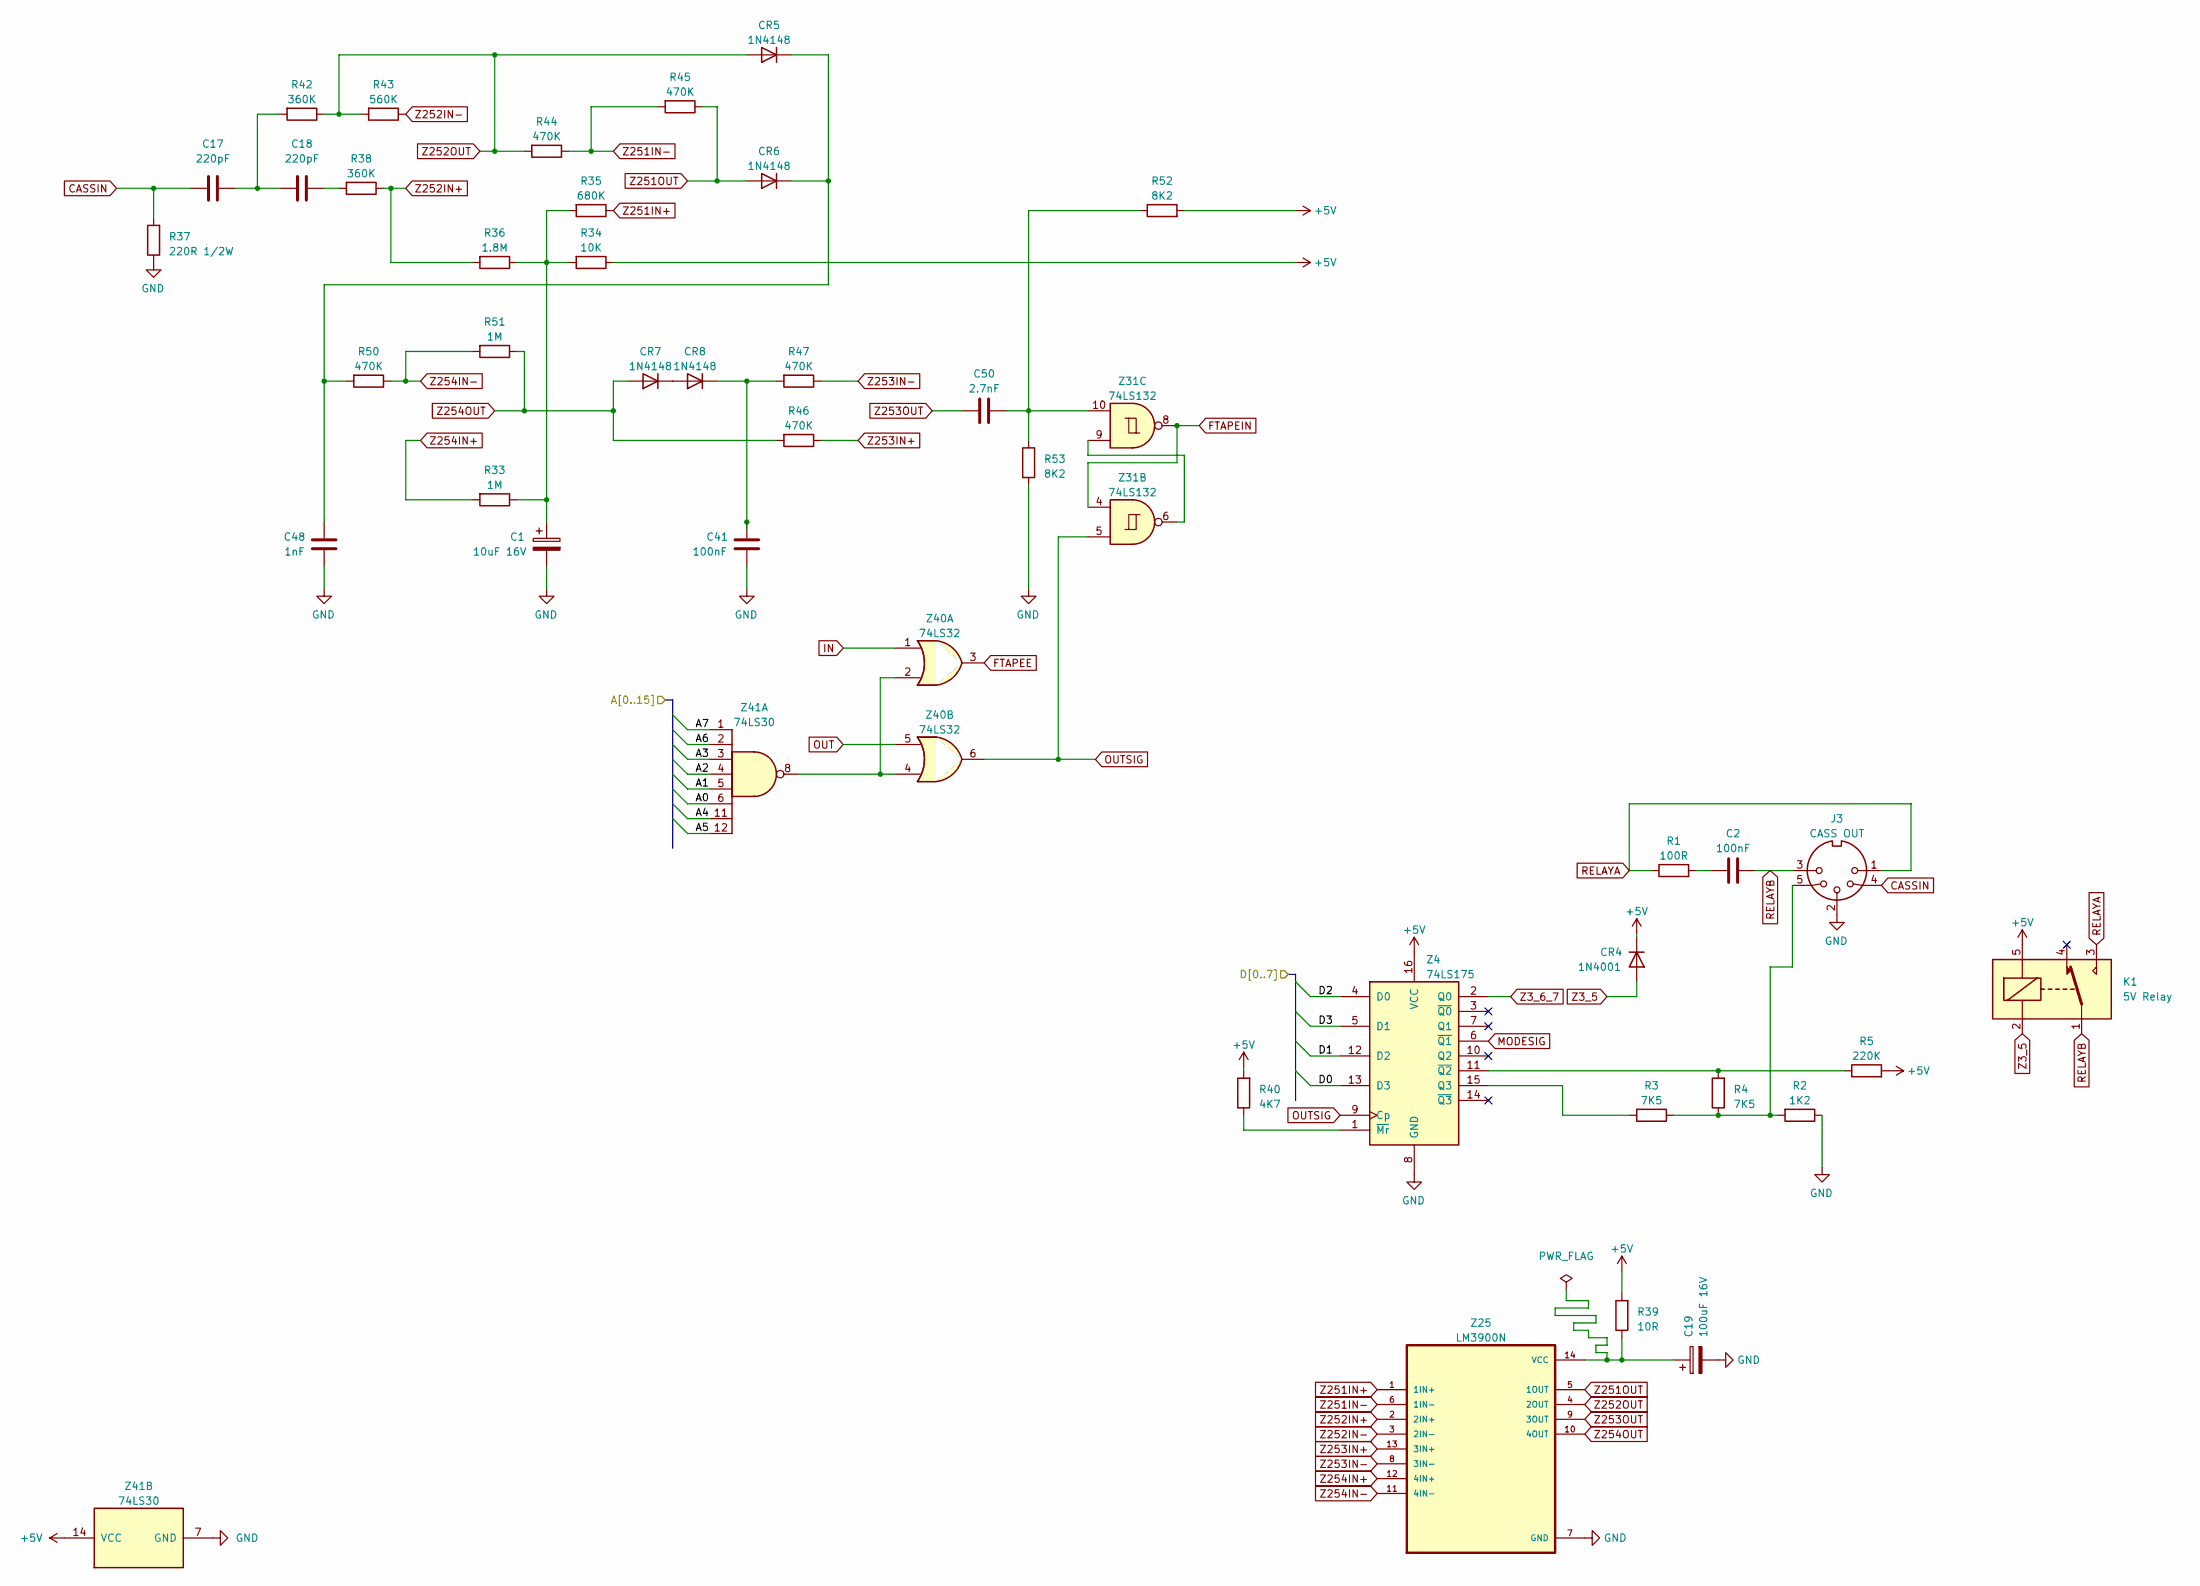
[picture p18: schematic TRS80IJP_TAPE.kicad_sch]

Parts:
C1: 10uF 16V; CP_Radial_D5.0mm_P2.50mm
C2, C41: 100nF; Ceramic Disc 5mm
C17, C18: 220pF; Ceramic Disc 5mm
C19: 100uF 16V; CP_Radial_P5.00mm
C48: 1nF; Ceramic Disc 5mm
C50: 2.7nF; Ceramic Disc 5mm
CR4: 1N4001; Diode 10.16mm
CR5, CR6, CR7, CR8: 1N4148; Diode 10.16mm
J3: CASS OUT; J3 - CASSETTE
K1: 5V Relay; K1 Relay
R1: 100R; Resistor 10.16mm
R2: 1K2; Resistor 10.16mm
R3, R4: 7K5; Resistor 10.16mm
R5: 220K; Resistor 10.16mm
R33, R51: 1M; Resistor 10.16mm
R34: 10K; Resistor 10.16mm
R35: 680K; Resistor 10.16mm
R36: 1.8M; Resistor 10.16mm
R37: 220R 1/2W; Resistor 15mm
R38, R42: 360K; Resistor 10.16mm
R39: 10R; Resistor 10.16mm
R40: 4K7; Resistor 10.16mm
R43: 560K; Resistor 10.16mm
R44, R45, R46, R47, R50: 470K; Resistor 10.16mm
R52, R53: 8K2; Resistor 10.16mm
Z4: 74LS175; DIP-16_W7.62mm
Z25: LM3900N; DIP-14_W7.62mm
Z31: 74LS132; DIP-14_W7.62mm
Z40: 74LS32; DIP-14_W7.62mm
Z41: 74LS30; DIP-14_W7.62mm

Connections:
+5V: CR4.1 (K), K1.5, R5.2, R34.1, R39.2, R40.2, R52.2, Z4.16 (VCC), Z41.14 (VCC)
A0: Z41.6
A1: Z41.5
A2: Z41.4
A3: Z41.3
A4: Z41.11
A5: Z41.12
A6: Z41.2
A7: Z41.1
CASSIN: C17.1, J3.4, R37.2
D0: Z4.13 (D3)
D1: Z4.12 (D2)
D2: Z4.4 (D0)
D3: Z4.5 (D1)
FTAPEE: Z40.3
FTAPEIN: Z31.4, Z31.8
GND: C1.2, C19.2, C41.1, C48.1, J3.2, R2.1, R37.1, R53.2, Z4.8 (GND), Z25.7 (GND), Z41.7 (GND)
IN: Z40.1
MODESIG: Z4.6 (~Q1)
unnamed: C1.1, R33.1, R34.2, R35.2, R36.1
unnamed: C2.1, R1.2
unnamed: C17.2, C18.1, R42.2
unnamed: C18.2, R38.2
unnamed: C19.1, R39.1, Z25.14 (VCC)
unnamed: C41.2, CR8.1 (K), R47.2
unnamed: C48.2, CR5.1 (K), CR6.1 (K), R50.2
unnamed: C50.2, R52.1, R53.1, Z31.10
unnamed: CR7.1 (K), CR8.2 (A)
unnamed: J3.5, R2.2, R3.1, R4.1
unnamed: R3.2, Z4.15 (Q3)
unnamed: R4.2, R5.1, Z4.11 (~Q2)
unnamed: R40.1, Z4.1 (~Mr)
unnamed: Z31.6, Z31.9
unnamed: Z40.2, Z40.4, Z41.8
OUT: Z40.5
OUTSIG: Z4.9 (Cp), Z31.5, Z40.6
RELAYA: J3.1, K1.3, R1.1
RELAYB: C2.2, J3.3, K1.1
Z3_5: CR4.2 (A), K1.2
Z3_6_7: Z4.2 (Q0)
Z251IN+: R35.1, Z25.1 (1IN+)
Z251IN-: R44.1, R45.2, Z25.6 (1IN-)
Z251OUT: CR6.2 (A), R45.1, Z25.5 (1OUT)
Z252IN+: R36.2, R38.1, Z25.2 (2IN+)
Z252IN-: R43.1, Z25.3 (2IN-)
Z252OUT: CR5.2 (A), R42.1, R43.2, R44.2, Z25.4 (2OUT)
Z253IN+: R46.1, Z25.13 (3IN+)
Z253IN-: R47.1, Z25.8 (3IN-)
Z253OUT: C50.1, Z25.9 (3OUT)
Z254IN+: R33.2, Z25.12 (4IN+)
Z254IN-: R50.1, R51.2, Z25.11 (4IN-)
Z254OUT: CR7.2 (A), R46.2, R51.1, Z25.10 (4OUT)
