Board-Folk/TRS80IJP/v1.1/Kicad/TRS80IJP_TIMING.kicad_sch

## KiCad design v1.1/Kicad/TRS80IJP_TIMING.kicad_sch (2023-09-25)

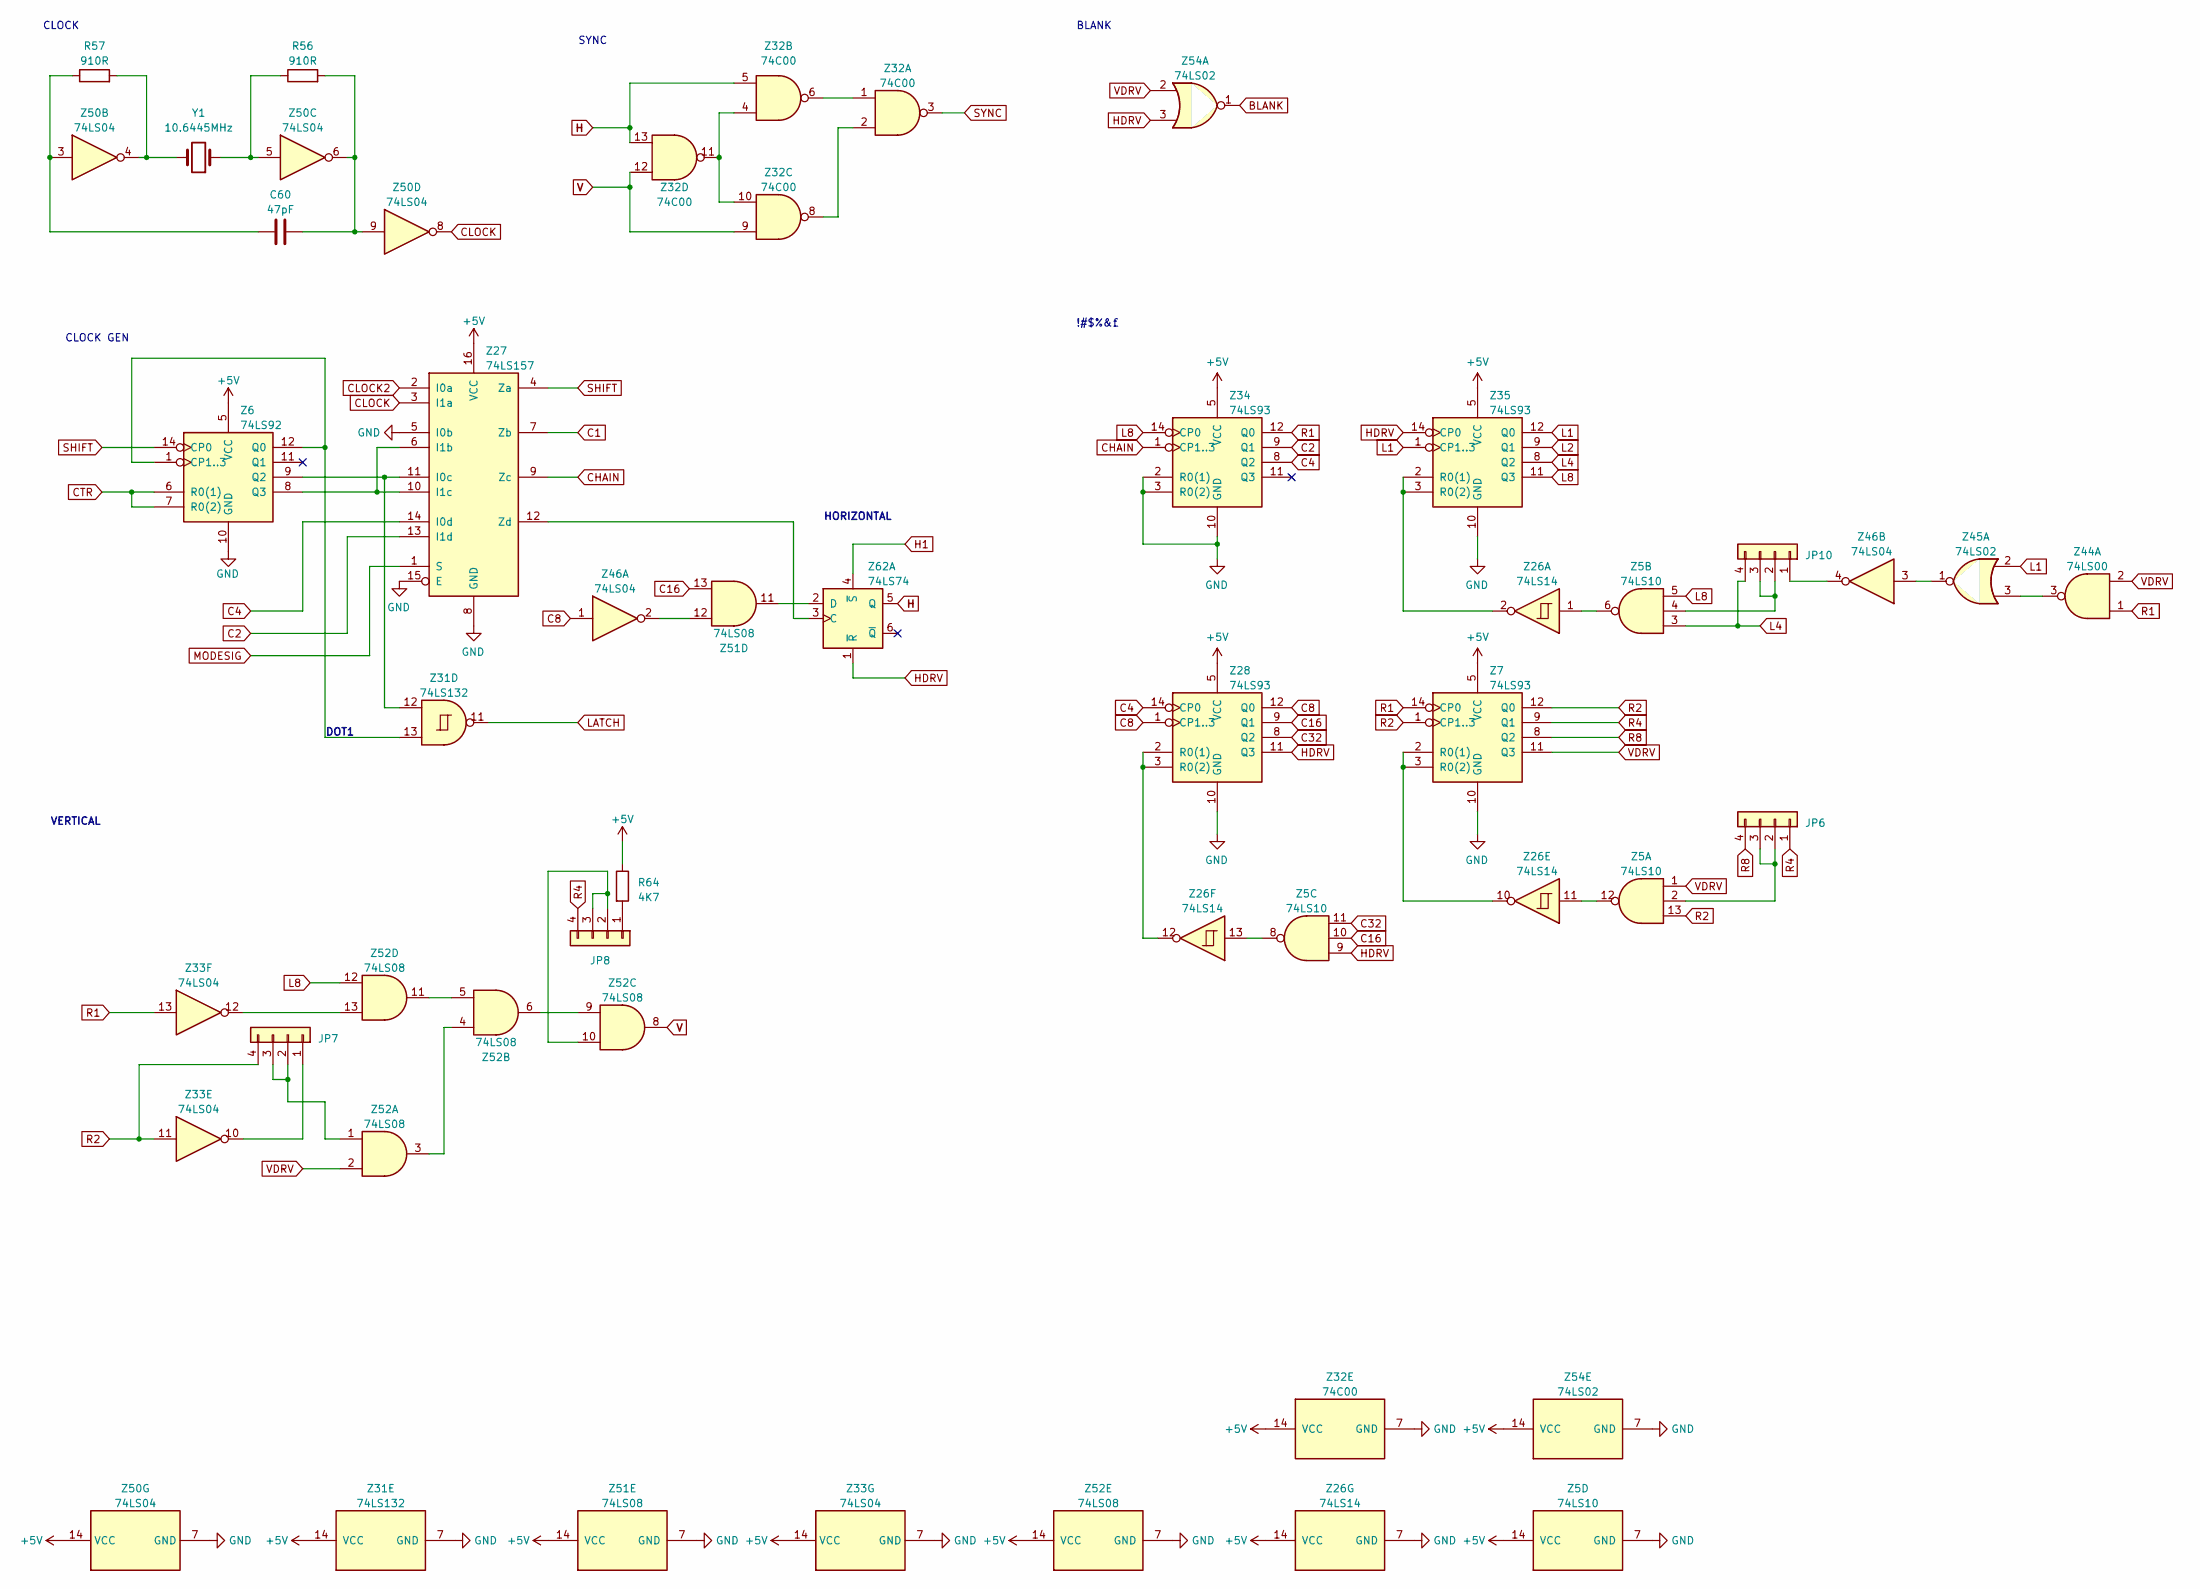
[picture p19: schematic TRS80IJP_TIMING.kicad_sch]

Parts:
C60: 47pF; Ceramic Disc 5mm
JP6, JP8, JP10: JP8; Double Wire Jumper
JP7: JP8; Double Wire Jumper - JP7
R56, R57: 910R; Resistor 10.16mm
R64: 4K7; Resistor 10.16mm
Y1: 10.6445MHz; Crystal
Z5: 74LS10; DIP-14_W7.62mm
Z6: 74LS92; DIP-14_W7.62mm
Z7, Z28, Z34, Z35: 74LS93; DIP-14_W7.62mm
Z26: 74LS14; DIP-14_W7.62mm
Z27: 74LS157; DIP-16_W7.62mm
Z31: 74LS132; DIP-14_W7.62mm
Z32: 74C00; DIP-14_W7.62mm
Z33, Z46, Z50: 74LS04; DIP-14_W7.62mm
Z44: 74LS00; DIP-14_W7.62mm
Z45, Z54: 74LS02; DIP-14_W7.62mm
Z51, Z52: 74LS08; DIP-14_W7.62mm
Z62: 74LS74; DIP-14_W7.62mm

Connections:
+5V: R64.1, Z5.14 (VCC), Z6.5 (VCC), Z7.5 (VCC), Z26.14 (VCC), Z27.16 (VCC), Z28.5 (VCC), Z31.14 (VCC), Z32.14 (VCC), Z33.14 (VCC), Z34.5 (VCC), Z35.5 (VCC), Z50.14 (VCC), Z51.14 (VCC), Z52.14 (VCC), Z54.14 (VCC)
BLANK: Z54.1
C1: Z27.7 (Zb)
C2: Z27.13 (I1d), Z34.9 (Q1)
C4: Z27.14 (I0d), Z28.14 (CP0), Z34.8 (Q2)
C8: Z28.1 (CP1..3), Z28.12 (Q0), Z46.1
C16: Z5.10, Z28.9 (Q1), Z51.13
C32: Z5.11, Z28.8 (Q2)
CHAIN: Z27.9 (Zc), Z34.1 (CP1..3)
CLOCK: Z27.3 (I1a), Z50.8
CLOCK2: Z27.2 (I0a)
CTR: Z6.6 (R0(1)), Z6.7 (R0(2))
GND: Z5.7 (GND), Z6.10 (GND), Z7.10 (GND), Z26.7 (GND), Z27.5 (I0b), Z27.8 (GND), Z27.15 (E), Z28.10 (GND), Z31.7 (GND), Z32.7 (GND), Z33.7 (GND), Z34.2 (R0(1)), Z34.3 (R0(2)), Z34.10 (GND), Z35.10 (GND), Z50.7 (GND), Z51.7 (GND), Z52.7 (GND), Z54.7 (GND)
H: Z32.5, Z32.13, Z62.5 (Q)
H1: Z62.4 (~S)
HDRV: Z5.9, Z28.11 (Q3), Z35.14 (CP0), Z54.3, Z62.1 (~R)
L1: Z35.1 (CP1..3), Z35.12 (Q0), Z45.2
L2: Z35.9 (Q1)
L4: JP10.4, Z5.3, Z35.8 (Q2)
L8: Z5.5, Z34.14 (CP0), Z35.11 (Q3), Z52.12
LATCH: Z31.11
MODESIG: Z27.1 (S)
unnamed: C60.1, R57.1, Z50.3
unnamed: C60.2, R56.2, Z50.6, Z50.9
unnamed: JP6.2, JP6.3, Z5.2
unnamed: JP7.1, Z33.10
unnamed: JP7.2, JP7.3, Z52.1
unnamed: JP8.1, R64.2
unnamed: JP8.2, JP8.3, Z52.10
unnamed: JP10.1, Z46.4
unnamed: JP10.2, JP10.3, Z5.4
unnamed: R56.1, Y1.1, Z50.5
unnamed: R57.2, Y1.2, Z50.4
unnamed: Z5.6, Z26.1
unnamed: Z26.2, Z35.2 (R0(1)), Z35.3 (R0(2))
unnamed: Z7.2 (R0(1)), Z7.3 (R0(2)), Z26.10
unnamed: Z5.12, Z26.11
unnamed: Z26.12, Z28.2 (R0(1)), Z28.3 (R0(2))
unnamed: Z5.8, Z26.13
unnamed: Z6.8 (Q3), Z27.6 (I1b), Z27.10 (I1c)
unnamed: Z6.9 (Q2), Z27.11 (I0c), Z31.12
unnamed: Z27.12 (Zd), Z62.3 (C)
unnamed: Z6.1 (CP1..3), Z6.12 (Q0), Z31.13
unnamed: Z32.1, Z32.6
unnamed: Z32.2, Z32.8
unnamed: Z32.4, Z32.10, Z32.11
unnamed: Z33.12, Z52.13
unnamed: Z44.3, Z45.3
unnamed: Z45.1, Z46.3
unnamed: Z46.2, Z51.12
unnamed: Z51.11, Z62.2 (D)
unnamed: Z52.3, Z52.4
unnamed: Z52.6, Z52.9
unnamed: Z52.5, Z52.11
R1: Z7.14 (CP0), Z33.13, Z34.12 (Q0), Z44.1
R2: JP7.4, Z5.13, Z7.1 (CP1..3), Z7.12 (Q0), Z33.11
R4: JP6.1, JP8.4, Z7.9 (Q1)
R8: JP6.4, Z7.8 (Q2)
SHIFT: Z6.14 (CP0), Z27.4 (Za)
SYNC: Z32.3
V: Z32.9, Z32.12, Z52.8
VDRV: Z5.1, Z7.11 (Q3), Z44.2, Z52.2, Z54.2

Notes on the sheet:
BLANK
VERTICAL
SYNC
DOT1
CLOCK
!#$%&£
CLOCK GEN
HORIZONTAL
