Board-Folk/TRS80IJP/v1.1/Kicad/TRS80IJP_VIDEO.kicad_sch

## KiCad design v1.1/Kicad/TRS80IJP_VIDEO.kicad_sch (2023-09-25)

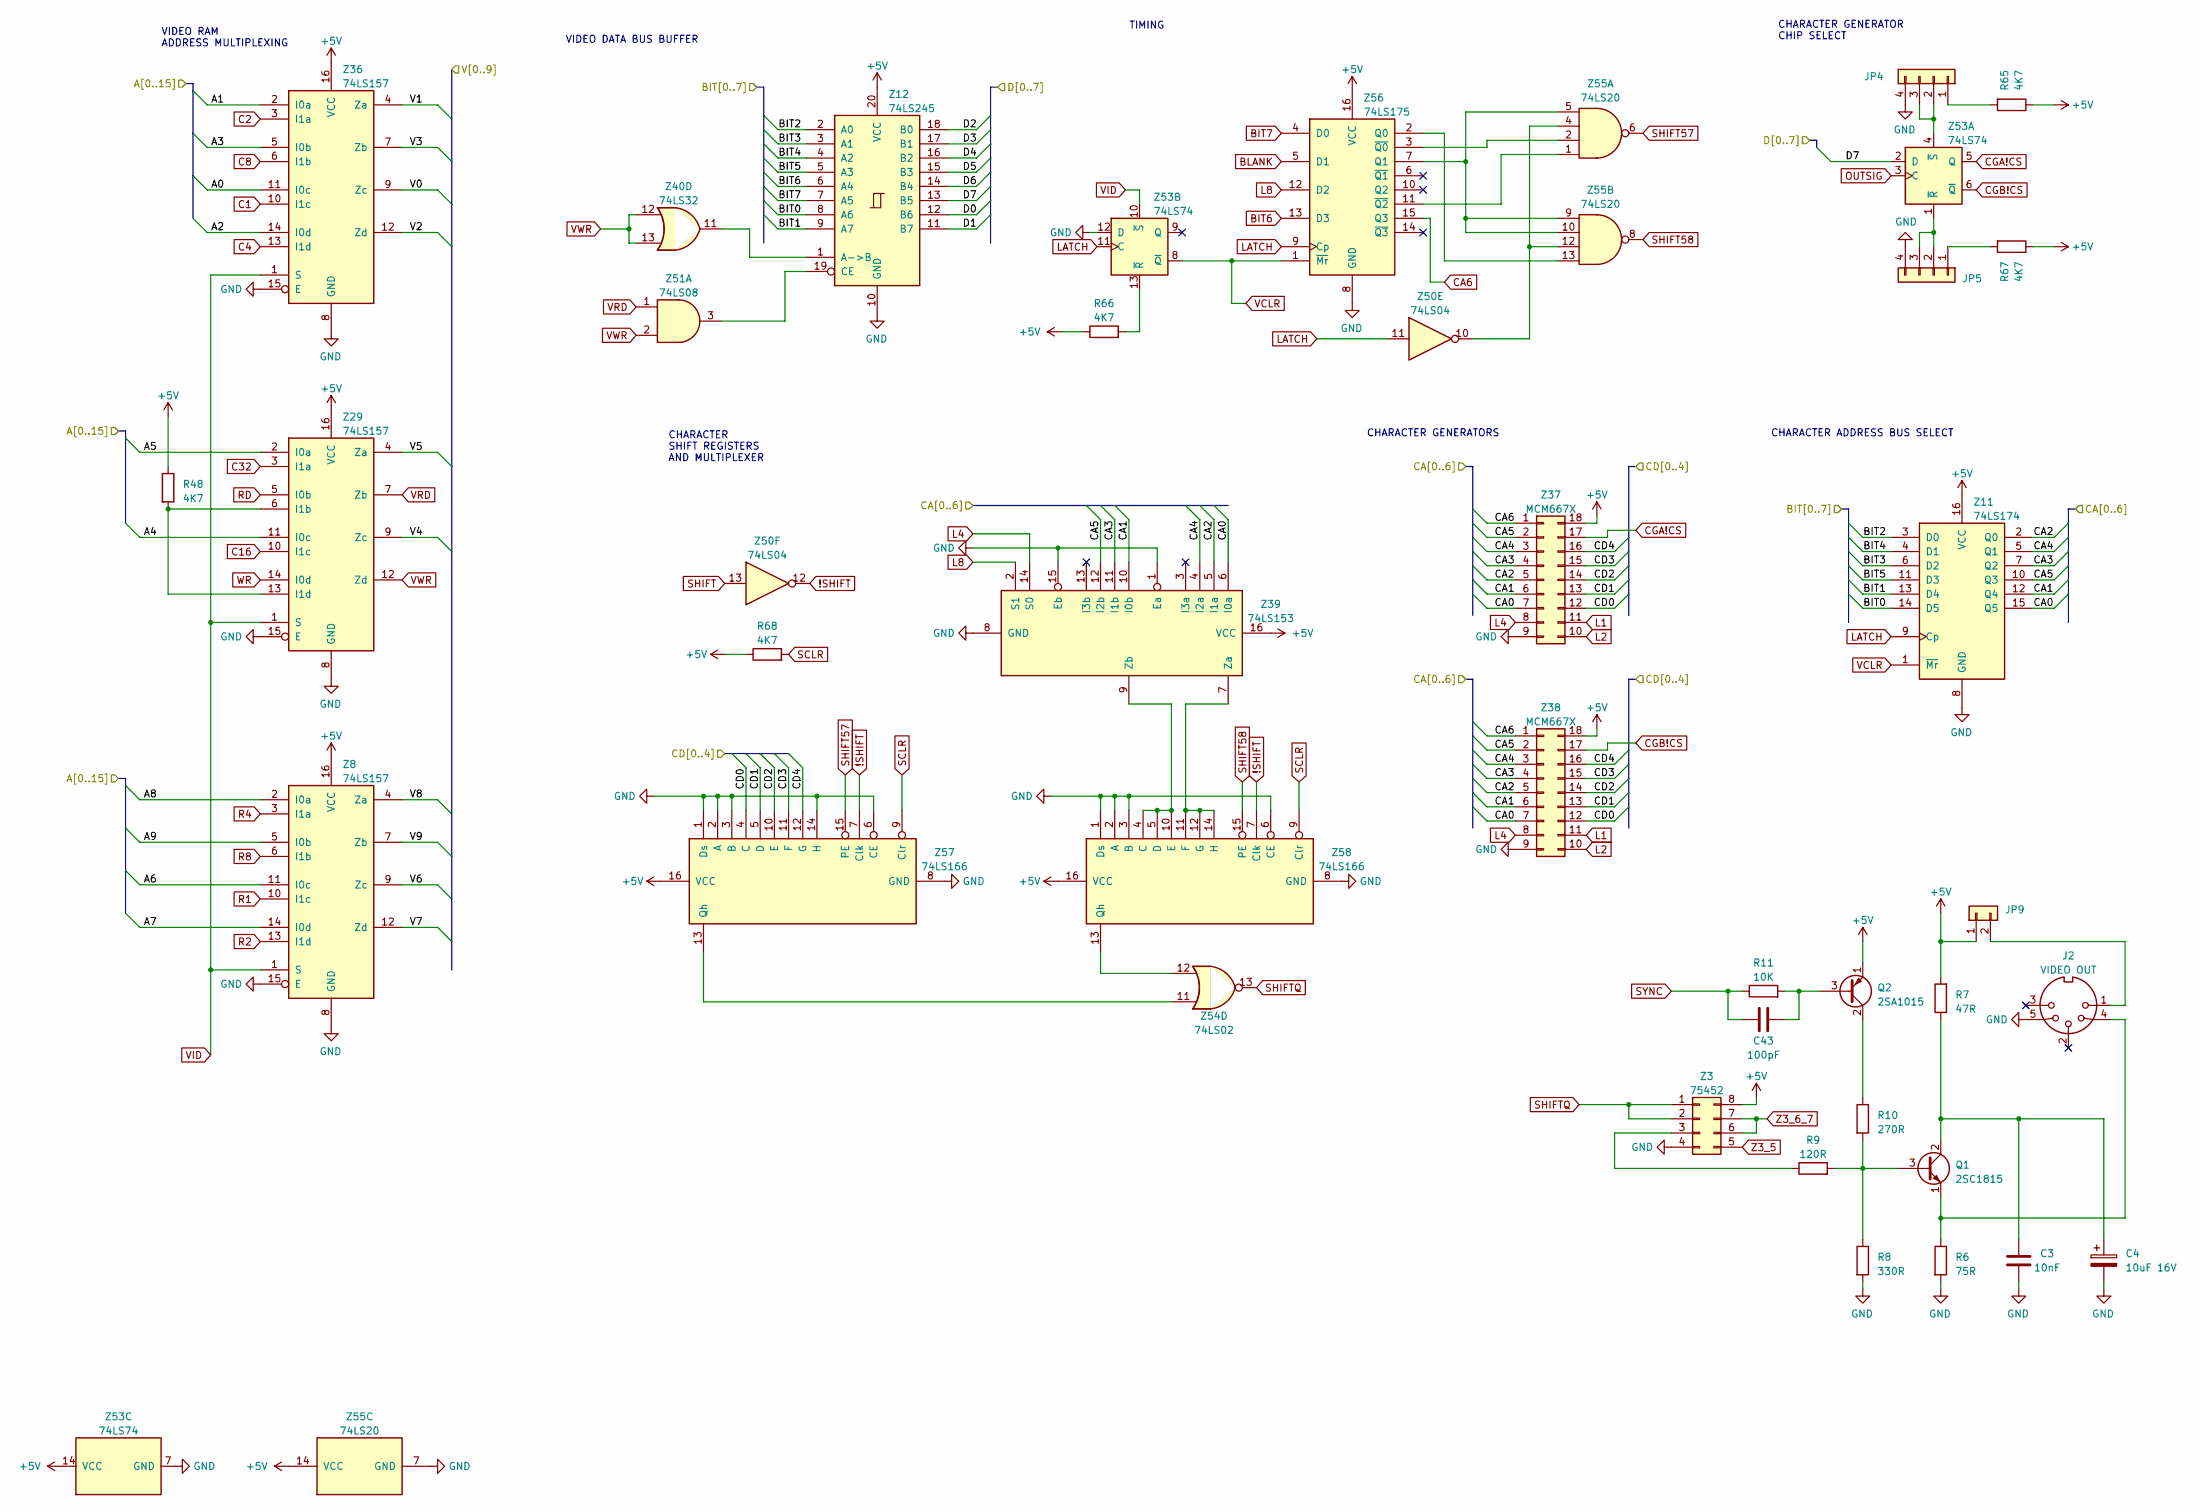
[picture p20: schematic TRS80IJP_VIDEO.kicad_sch]

Parts:
C3: 10nF; Ceramic Disc 5mm
C4: 10uF 16V; CP_Radial_D5.0mm_P2.50mm
C43: 100pF; Ceramic Disc 2.5mm
J2: VIDEO OUT; J2 - VIDEO OUT
JP4, JP5: JP8; Double Wire Jumper
JP9: JP9; Wire Jumper
Q1: 2SC1815; TO-92_Transistor
Q2: 2SA1015; TO-92_Transistor
R6: 75R; Resistor 10.16mm
R7: 47R; Resistor 10.16mm
R8: 330R; Resistor 10.16mm
R9: 120R; Resistor 10.16mm
R10: 270R; Resistor 10.16mm
R11: 10K; Resistor 10.16mm
R48, R65, R66, R67, R68: 4K7; Resistor 10.16mm
Z3: 75452; DIP-8_W7.62mm
Z8, Z29, Z36: 74LS157; DIP-16_W7.62mm
Z11: 74LS174; DIP-16_W7.62mm
Z12: 74LS245; DIP-20_W7.62mm
Z37, Z38: MCM667X; DIP-18_W7.62mm
Z39: 74LS153; DIP-16_W7.62mm
Z40: 74LS32; DIP-14_W7.62mm
Z50: 74LS04; DIP-14_W7.62mm
Z51: 74LS08; DIP-14_W7.62mm
Z53: 74LS74; DIP-14_W7.62mm
Z54: 74LS02; DIP-14_W7.62mm
Z55: 74LS20; DIP-14_W7.62mm
Z56: 74LS175; DIP-16_W7.62mm
Z57, Z58: 74LS166; DIP-16_W7.62mm

Connections:
!SHIFT: Z50.12, Z57.7 (Clk), Z58.7 (Clk)
+5V: JP9.1, Q2.1 (E), R7.2, R48.1, R65.1, R66.1, R67.1, R68.1, Z3.8, Z8.16 (VCC), Z11.16 (VCC), Z12.20 (VCC), Z29.16 (VCC), Z36.16 (VCC), Z37.18, Z38.18, Z39.16 (VCC), Z53.14 (VCC), Z55.14 (VCC), Z56.16 (VCC), Z57.16 (VCC), Z58.16 (VCC)
A0: Z36.11 (I0c)
A1: Z36.2 (I0a)
A2: Z36.14 (I0d)
A3: Z36.5 (I0b)
A4: Z29.11 (I0c)
A5: Z29.2 (I0a)
A6: Z8.11 (I0c)
A7: Z8.14 (I0d)
A8: Z8.2 (I0a)
A9: Z8.5 (I0b)
BIT0: Z11.14 (D5), Z12.8 (A6)
BIT1: Z11.13 (D4), Z12.9 (A7)
BIT2: Z11.3 (D0), Z12.2 (A0)
BIT3: Z11.6 (D2), Z12.3 (A1)
BIT4: Z11.4 (D1), Z12.4 (A2)
BIT5: Z11.11 (D3), Z12.5 (A3)
BIT6: Z12.6 (A4), Z56.13 (D3)
BIT7: Z12.7 (A5), Z56.4 (D0)
BLANK: Z56.5 (D1)
C1: Z36.10 (I1c)
C2: Z36.3 (I1a)
C4: Z36.13 (I1d)
C8: Z36.6 (I1b)
C16: Z29.10 (I1c)
C32: Z29.3 (I1a)
CA0: Z11.15 (Q5), Z37.7, Z38.7, Z39.6 (I0a)
CA1: Z11.12 (Q4), Z37.6, Z38.6, Z39.10 (I0b)
CA2: Z11.2 (Q0), Z37.5, Z38.5, Z39.5 (I1a)
CA3: Z11.7 (Q2), Z37.4, Z38.4, Z39.11 (I1b)
CA4: Z11.5 (Q1), Z37.3, Z38.3, Z39.4 (I2a)
CA5: Z11.10 (Q3), Z37.2, Z38.2, Z39.12 (I2b)
CA6: Z37.1, Z38.1, Z56.15 (Q3)
CD0: Z37.12, Z38.12, Z57.4 (C)
CD1: Z37.13, Z38.13, Z57.5 (D)
CD2: Z37.14, Z38.14, Z57.10 (E)
CD3: Z37.15, Z38.15, Z57.11 (F)
CD4: Z37.16, Z38.16, Z57.12 (G)
CGA!CS: Z37.17, Z53.5 (Q)
CGB!CS: Z38.17, Z53.6 (~Q)
D0: Z12.12 (B6)
D1: Z12.11 (B7)
D2: Z12.18 (B0)
D3: Z12.17 (B1)
D4: Z12.16 (B2)
D5: Z12.15 (B3)
D6: Z12.14 (B4)
D7: Z12.13 (B5), Z53.2 (D)
GND: C3.2, C4.2, J2.5, JP4.4, JP5.4, R6.2, R8.2, Z3.4, Z8.8 (GND), Z8.15 (E), Z11.8 (GND), Z12.10 (GND), Z29.8 (GND), Z29.15 (E), Z36.8 (GND), Z36.15 (E), Z37.9, Z38.9, Z39.1 (Ea), Z39.8 (GND), Z39.15 (Eb), Z53.7 (GND), Z53.12 (D), Z55.7 (GND), Z56.8 (GND), Z57.1 (Ds), Z57.2 (A), Z57.3 (B), Z57.6 (CE), Z57.8 (GND), Z57.14 (H), Z58.1 (Ds), Z58.2 (A), Z58.3 (B), Z58.6 (CE), Z58.8 (GND)
L1: Z37.11, Z38.11
L2: Z37.10, Z38.10
L4: Z37.8, Z38.8, Z39.14 (S0)
L8: Z39.2 (S1), Z56.12 (D2)
LATCH: Z11.9 (Cp), Z50.11, Z53.11 (C), Z56.9 (Cp)
unnamed: C3.1, C4.1, Q1.2 (C), R7.1
unnamed: C43.1, Q2.3 (B), R11.2
unnamed: J2.1, JP9.2
unnamed: J2.4, Q1.1 (E), R6.1
unnamed: JP4.1, R65.2
unnamed: JP4.2, JP4.3, Z53.4 (~S)
unnamed: JP5.1, R67.2
unnamed: JP5.2, JP5.3, Z53.1 (~R)
unnamed: Q1.3 (B), R8.1, R9.2, R10.2
unnamed: Q2.2 (C), R10.1
unnamed: R9.1, Z3.3
unnamed: R48.2, Z29.6 (I1b), Z29.13 (I1d)
unnamed: R66.2, Z53.13 (~R)
unnamed: Z12.1 (A->B), Z40.11
unnamed: Z12.19 (CE), Z51.3
unnamed: Z39.7 (Za), Z58.11 (F), Z58.12 (G), Z58.14 (H)
unnamed: Z39.9 (Zb), Z58.4 (C), Z58.5 (D), Z58.10 (E)
unnamed: Z50.10, Z55.4, Z55.12
unnamed: Z54.11, Z57.13 (Qh)
unnamed: Z54.12, Z58.13 (Qh)
unnamed: Z55.1, Z56.11 (~Q2)
unnamed: Z55.2, Z56.3 (~Q0)
unnamed: Z55.5, Z55.9, Z55.10, Z56.7 (Q1)
unnamed: Z55.13, Z56.2 (Q0)
OUTSIG: Z53.3 (C)
R1: Z8.10 (I1c)
R2: Z8.13 (I1d)
R4: Z8.3 (I1a)
R8: Z8.6 (I1b)
RD: Z29.5 (I0b)
SCLR: R68.2, Z57.9 (Clr), Z58.9 (Clr)
SHIFT: Z50.13
SHIFT57: Z55.6, Z57.15 (PE)
SHIFT58: Z55.8, Z58.15 (PE)
SHIFTQ: Z3.1, Z3.2, Z54.13
SYNC: C43.2, R11.1
V0: Z36.9 (Zc)
V1: Z36.4 (Za)
V2: Z36.12 (Zd)
V3: Z36.7 (Zb)
V4: Z29.9 (Zc)
V5: Z29.4 (Za)
V6: Z8.9 (Zc)
V7: Z8.12 (Zd)
V8: Z8.4 (Za)
V9: Z8.7 (Zb)
VCLR: Z11.1 (~Mr), Z53.8 (~Q), Z56.1 (~Mr)
VID: Z8.1 (S), Z29.1 (S), Z36.1 (S), Z53.10 (~S)
VRD: Z29.7 (Zb), Z51.1
VWR: Z29.12 (Zd), Z40.12, Z40.13, Z51.2
WR: Z29.14 (I0d)
Z3_5: Z3.5
Z3_6_7: Z3.6, Z3.7

Notes on the sheet:
CHARACTER GENERATORS
VIDEO RAM ADDRESS MULTIPLEXING
CHARACTER ADDRESS BUS SELECT
TIMING
CHARACTER GENERATOR CHIP SELECT
VIDEO DATA BUS BUFFER
CHARACTER SHIFT REGISTERS AND MULTIPLEXER
